oldgerman/SAU-G0/Data/Images/20220714_SAU-G0-GL_9小时500+次采集.png

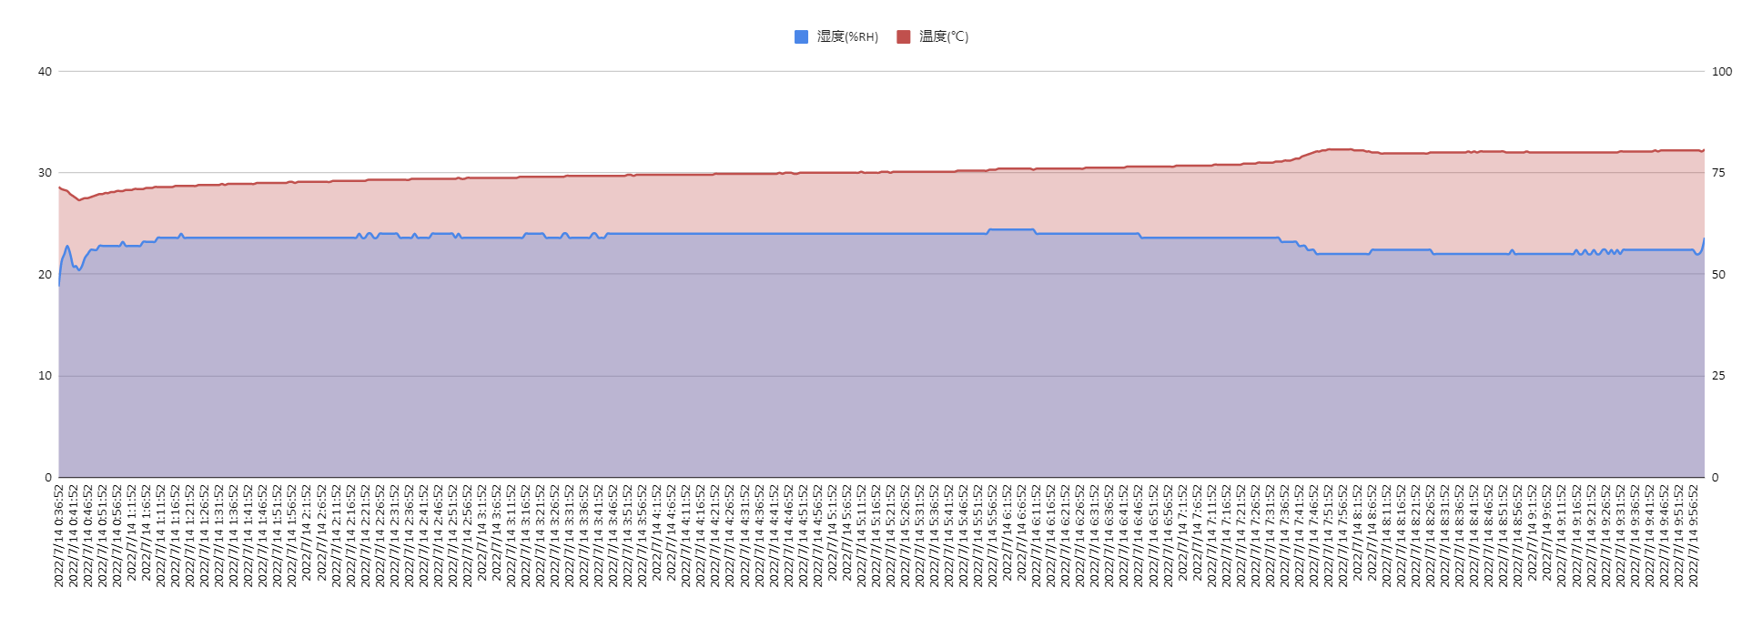
Data/Images/20220714_SAU-G0-GL_9小时500+次采集.png
