oldgerman/SAU-G0/Data/Images/20240409-20240522_SAU-G0-PL_43天2000+次采集2.png

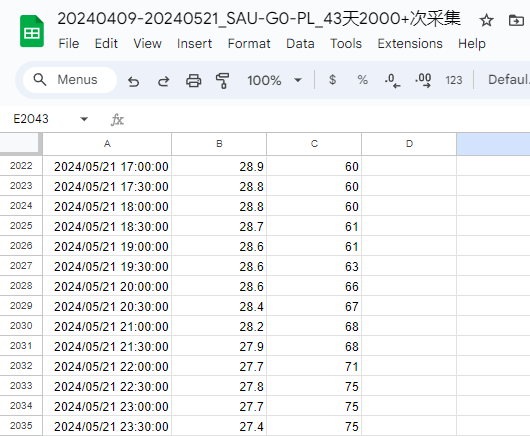
Data/Images/20240409-20240522_SAU-G0-PL_43天2000+次采集2.png
