oldgerman/SAU-G0/Data/Images/20240830-20240913_SAU-G0-PL_14天2043次采集.png

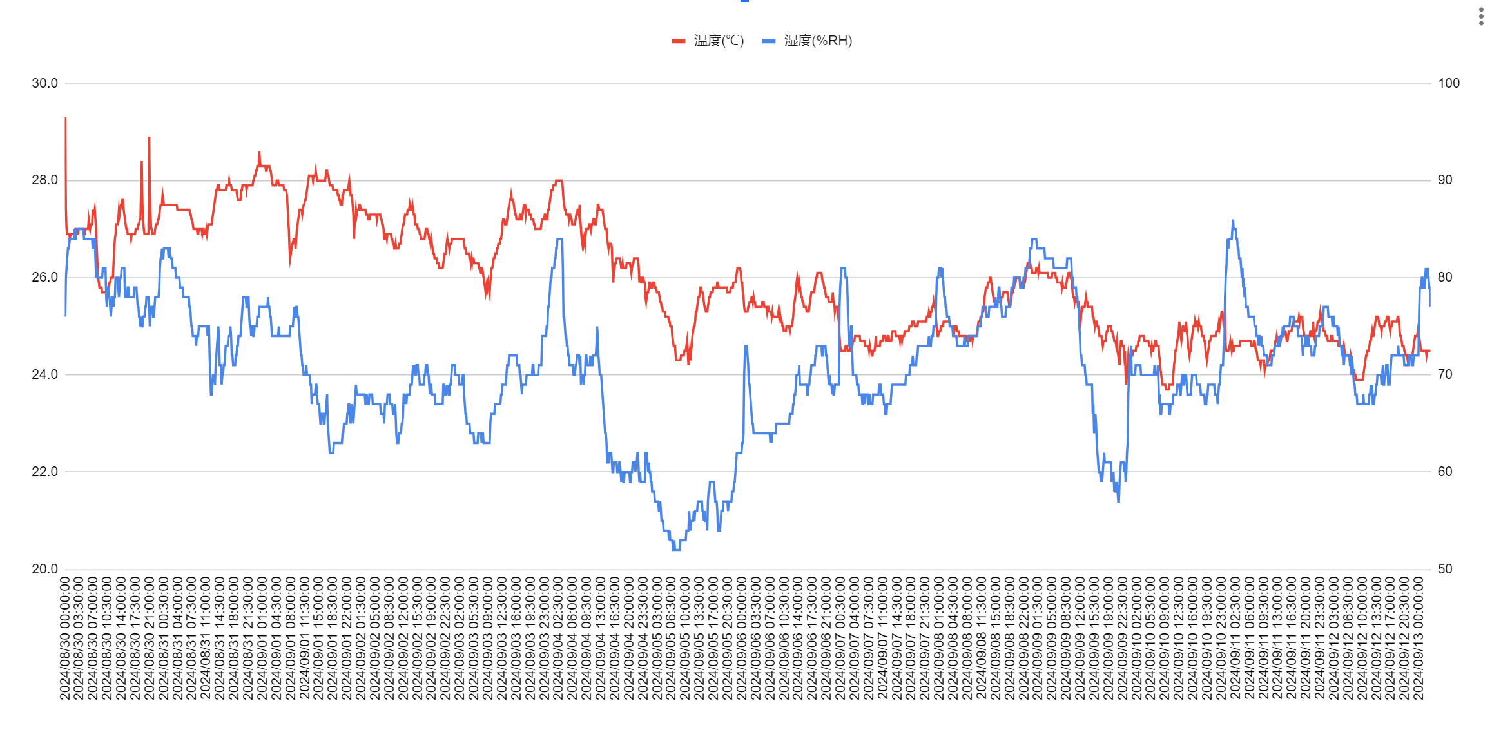
Data/Images/20240830-20240913_SAU-G0-PL_14天2043次采集.png
