oldgerman/SAU-G0/Data/Images/折线图选择数据时Invalid报错的原因是数据是文本，没有格式化为数字(1).png

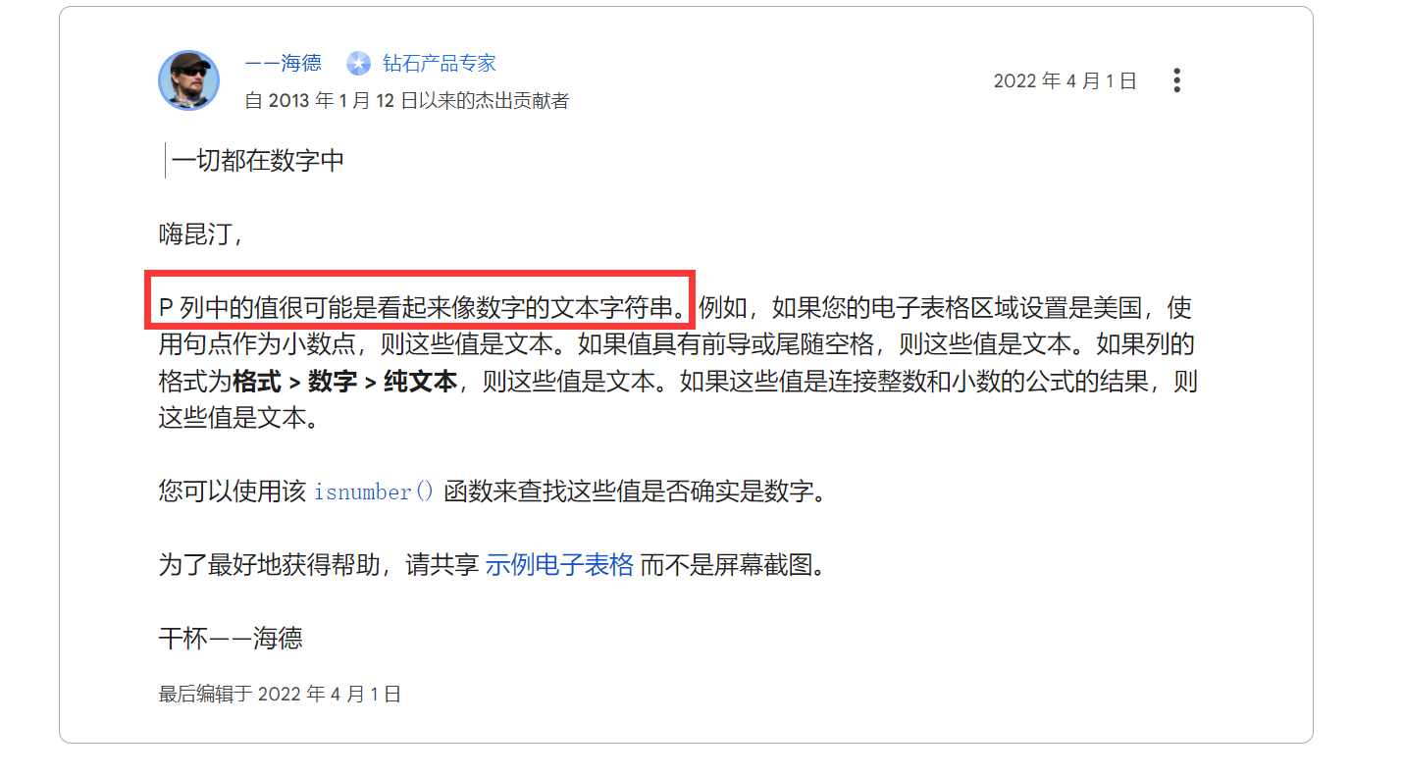
Data/Images/折线图选择数据时Invalid报错的原因是数据是文本，没有格式化为数字(1).png
