oldgerman/SAU-G0/Hardware/Datasheets/Diode/02_schaltplan_usb_ve-810x435-c-default.webp

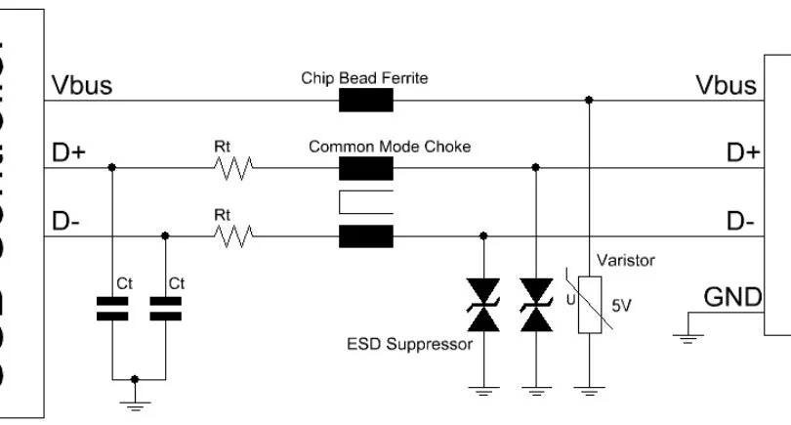
Hardware/Datasheets/Diode/02_schaltplan_usb_ve-810x435-c-default.webp
