oldgerman/SAU-G0/Hardware/Datasheets/Diode/2019-08-06_8-22-07.webp

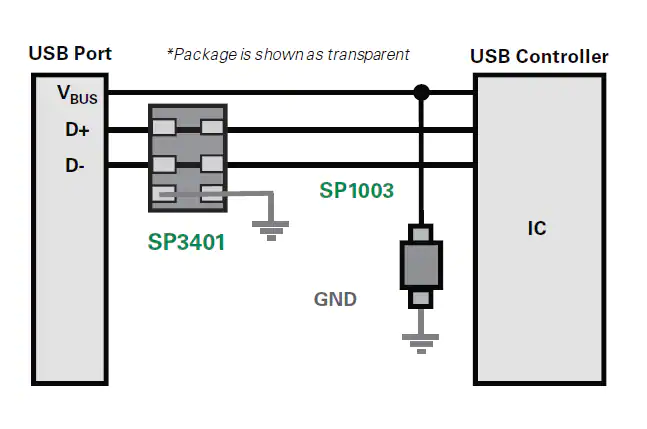
Hardware/Datasheets/Diode/2019-08-06_8-22-07.webp
