oldgerman/SAU-G0/Hardware/Datasheets/Diode/images.jpg

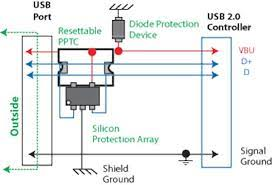
Hardware/Datasheets/Diode/images.jpg
