oldgerman/SAU-G0/Hardware/Datasheets/Diode/USB_2.0_Protection.jpg

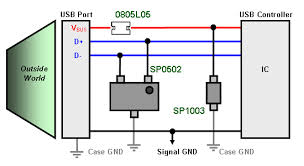
Hardware/Datasheets/Diode/USB_2.0_Protection.jpg
