oldgerman/SAU-G0/Hardware/Datasheets/Diode/vKJi6.png

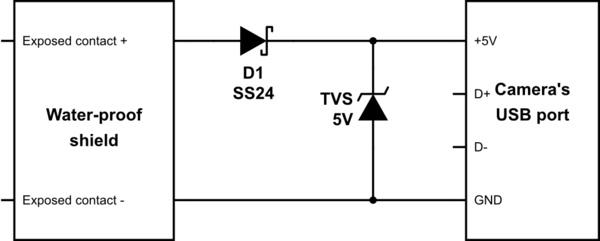
Hardware/Datasheets/Diode/vKJi6.png
