oldgerman/SAU-G0/Hardware/Datasheets/EEPROM/意法半导体串行接口的EEPROM m24c、M95、m93c特性.jpg

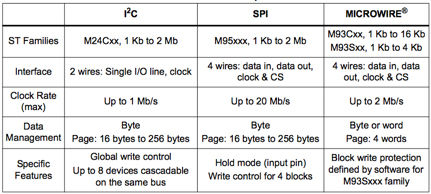
Hardware/Datasheets/EEPROM/意法半导体串行接口的EEPROM m24c、M95、m93c特性.jpg
