oldgerman/SAU-G0/Hardware/Datasheets/oled 0.66 16pin SPI/0.66 SSD1306 oled 尺寸图.jpg

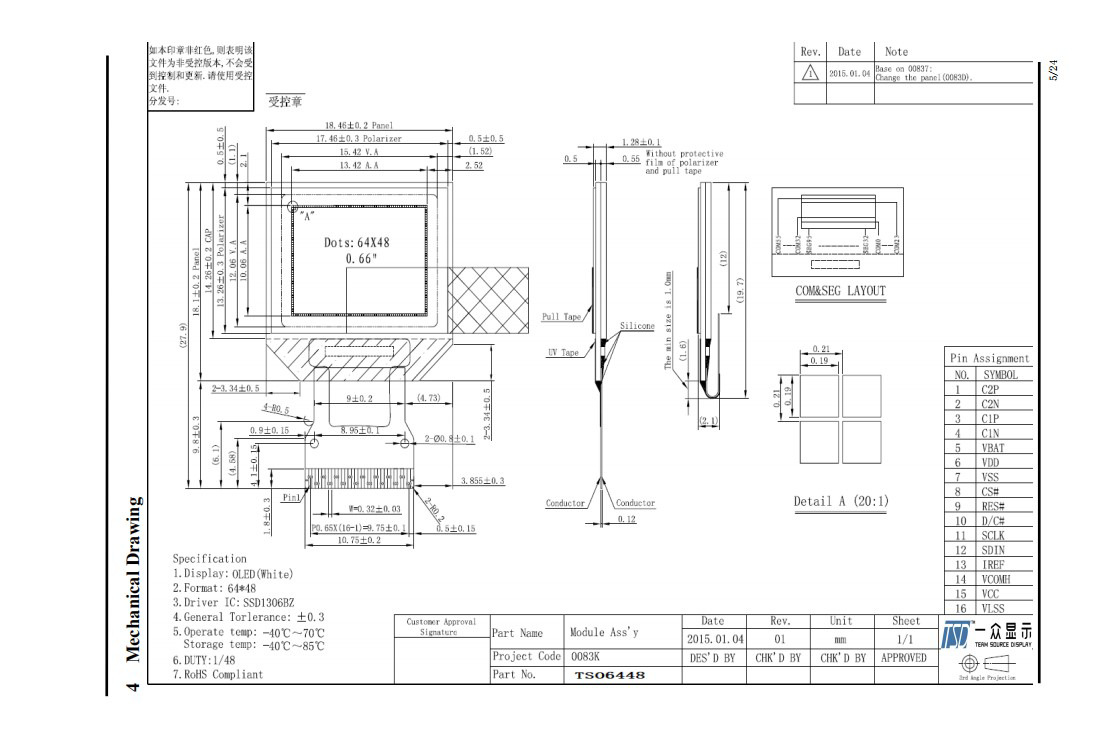
Hardware/Datasheets/oled 0.66 16pin SPI/0.66 SSD1306 oled 尺寸图.jpg
