oldgerman/SAU-G0/Hardware/Datasheets/oled 0.66 16pin SPI/外围电路.PNG

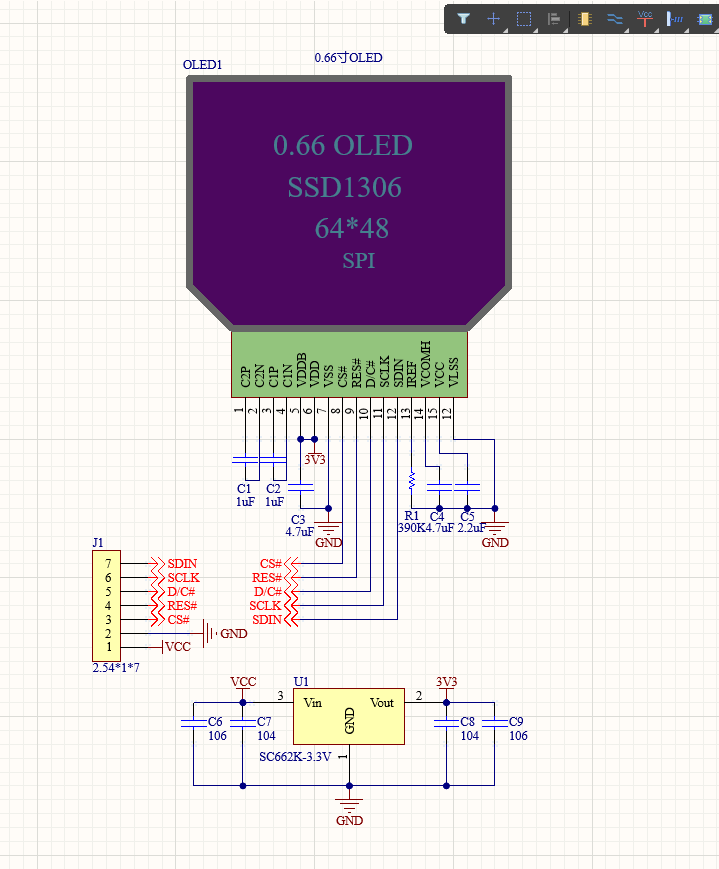
Hardware/Datasheets/oled 0.66 16pin SPI/外围电路.PNG
