oldgerman/SAU-G0/Hardware/Datasheets/RTC/DS3231/DS3231+EEPROM.png

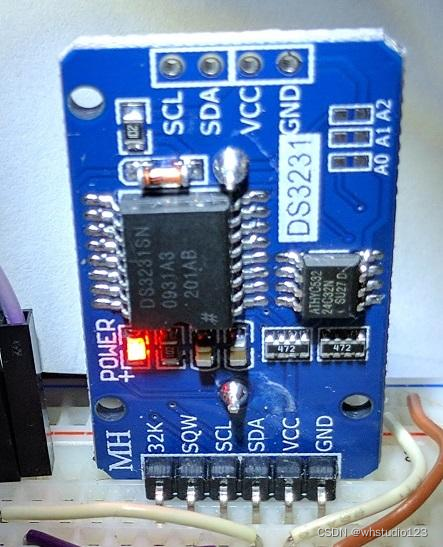
Hardware/Datasheets/RTC/DS3231/DS3231+EEPROM.png
