oldgerman/SAU-G0/Hardware/Datasheets/RTC/DS3231/images.jpg

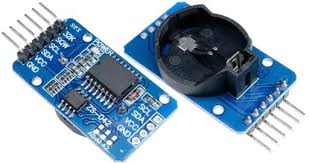
Hardware/Datasheets/RTC/DS3231/images.jpg
