oldgerman/SAU-G0/Hardware/Datasheets/RTC/PCF2129/FDK可充电电池_ML614R-TT31.png

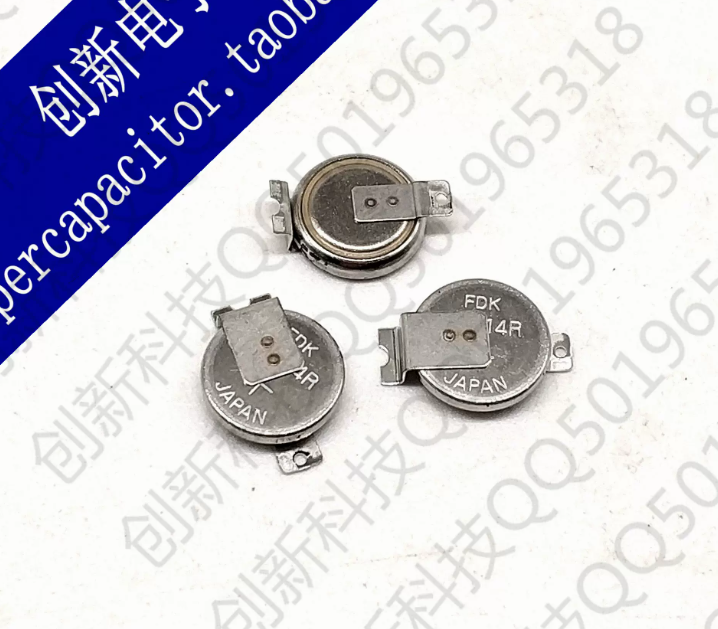
Hardware/Datasheets/RTC/PCF2129/FDK可充电电池_ML614R-TT31.png
