oldgerman/SAU-G0/Hardware/Datasheets/RTC/PCF2129/FDK可充电电池_ML系列产品线.png

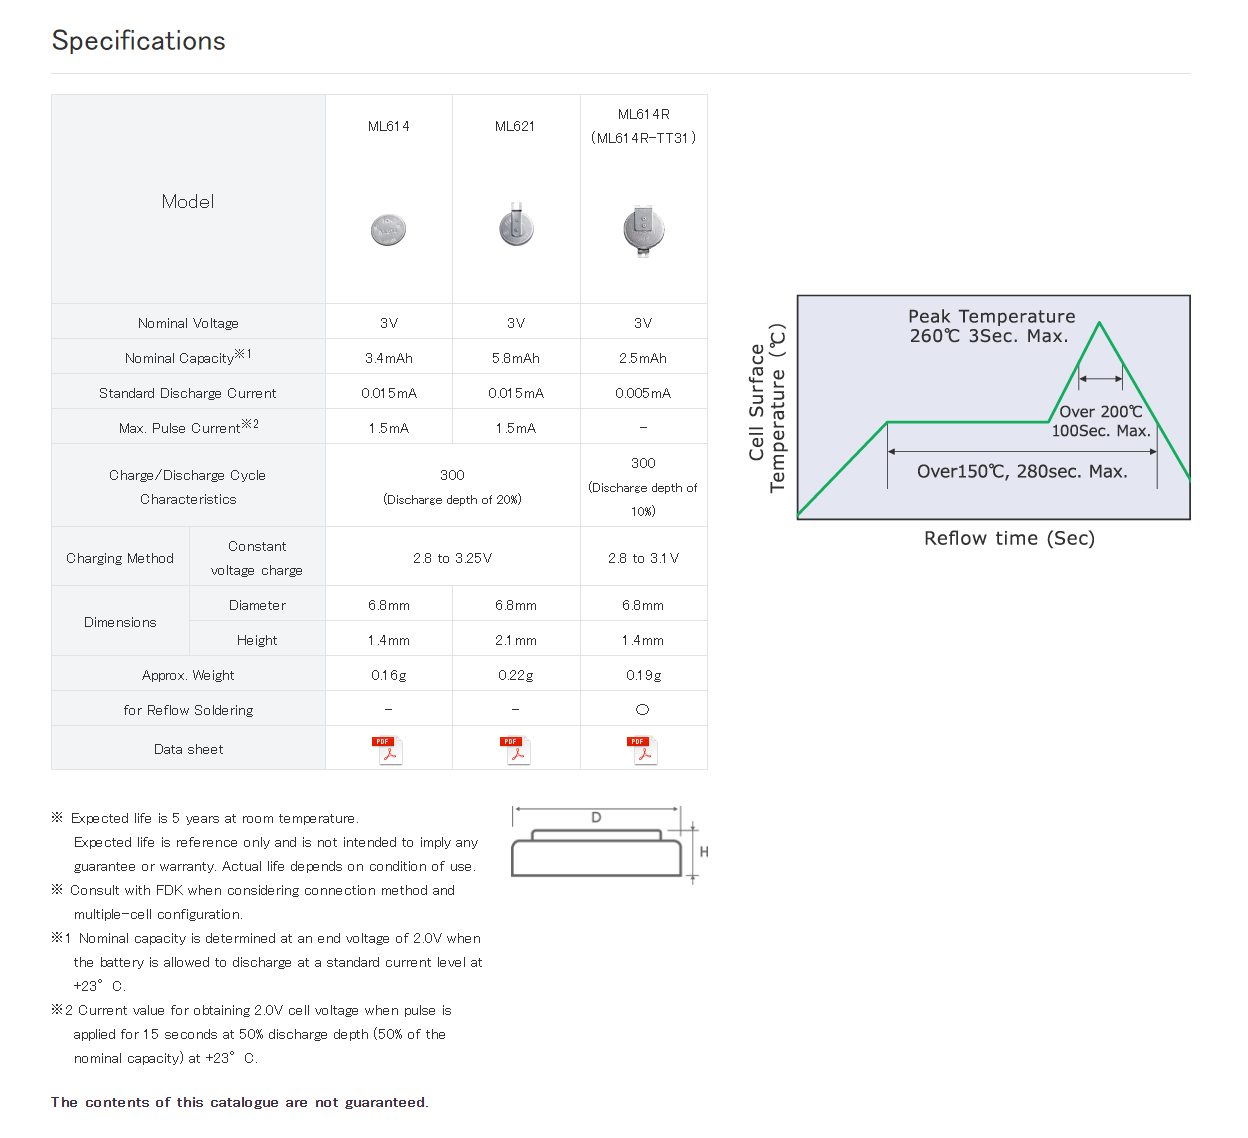
Hardware/Datasheets/RTC/PCF2129/FDK可充电电池_ML系列产品线.png
