oldgerman/SAU-G0/Hardware/Datasheets/RTC/PCF2129/image-1438068521577.jpg

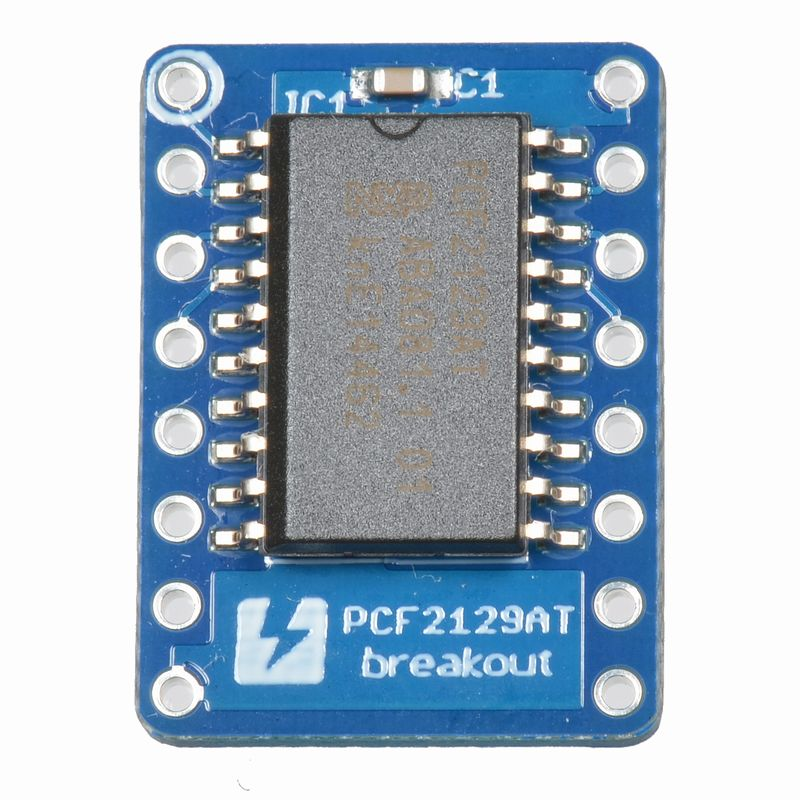
Hardware/Datasheets/RTC/PCF2129/image-1438068521577.jpg
