oldgerman/SAU-G0/Hardware/Datasheets/RTC/PCF2129/JST 614 Battery Holder, Button Contact.png

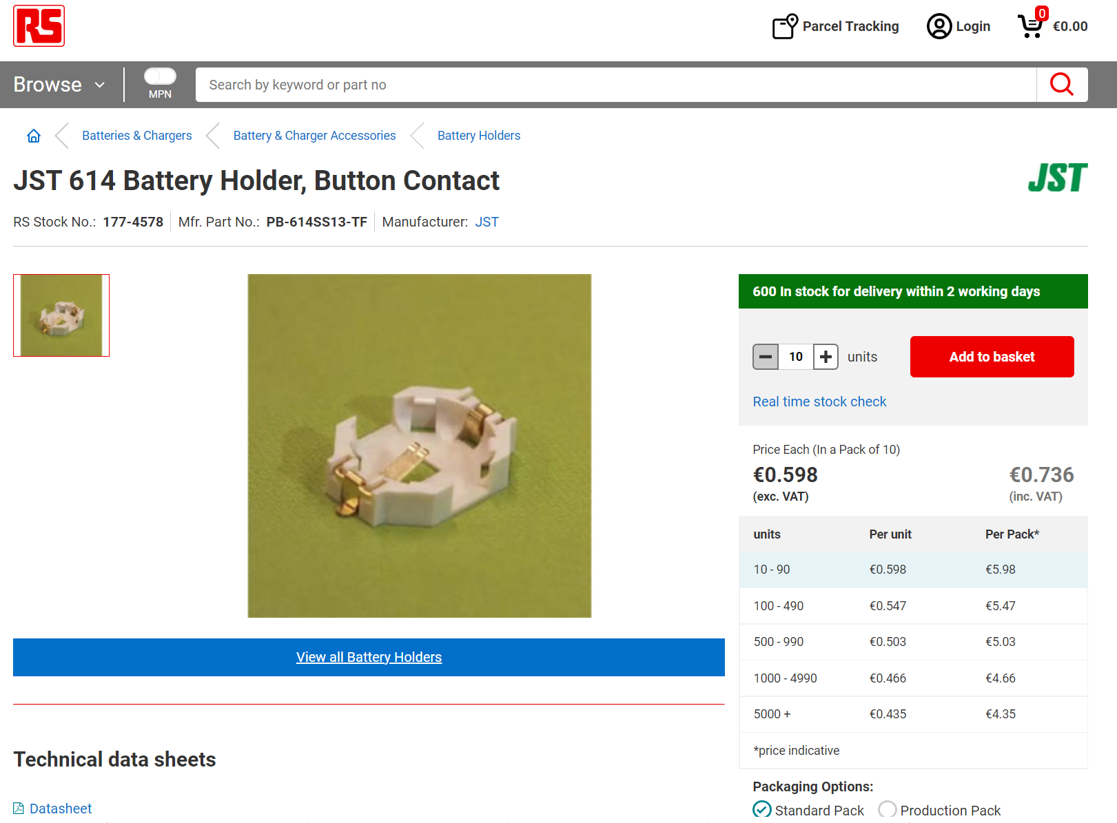
Hardware/Datasheets/RTC/PCF2129/JST 614 Battery Holder, Button Contact.png
