oldgerman/SAU-G0/Hardware/Datasheets/RTC/PCF2129/MS518SE-patch-connector.jpg

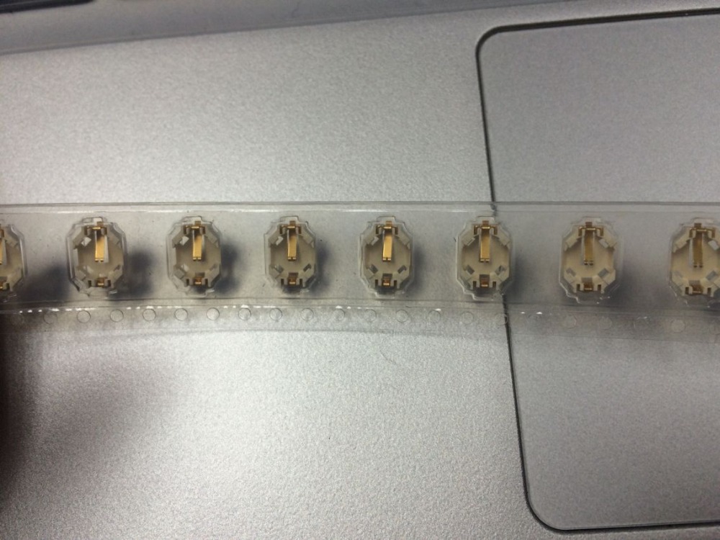
Hardware/Datasheets/RTC/PCF2129/MS518SE-patch-connector.jpg
