oldgerman/SAU-G0/Hardware/Datasheets/RTC/PCF2129/MS518SE-PCB焊接-注意电池下方禁止布线区.jpg

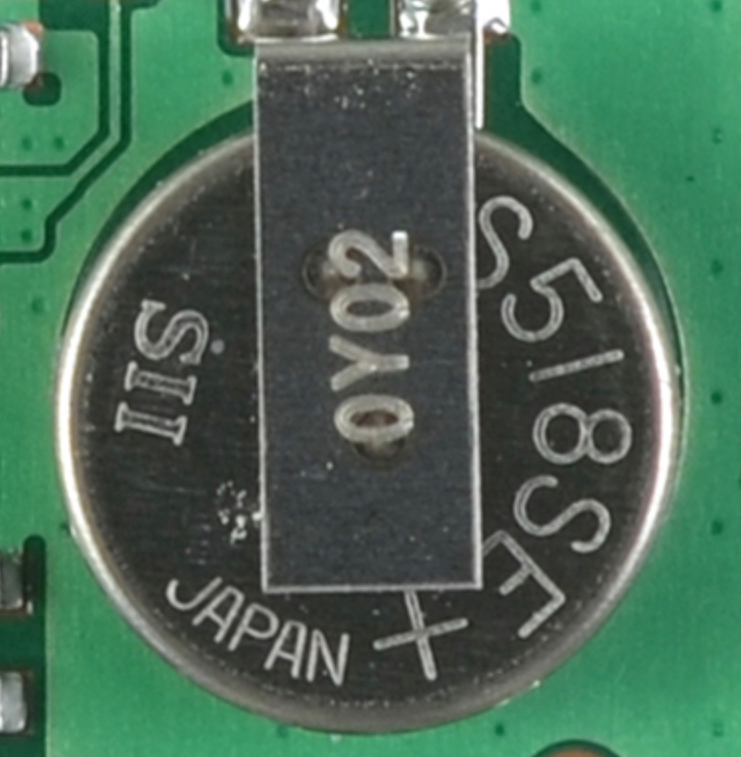
Hardware/Datasheets/RTC/PCF2129/MS518SE-PCB焊接-注意电池下方禁止布线区.jpg
