oldgerman/SAU-G0/Hardware/Datasheets/RTC/PCF2129/MS518SE背面焊盘.jpg

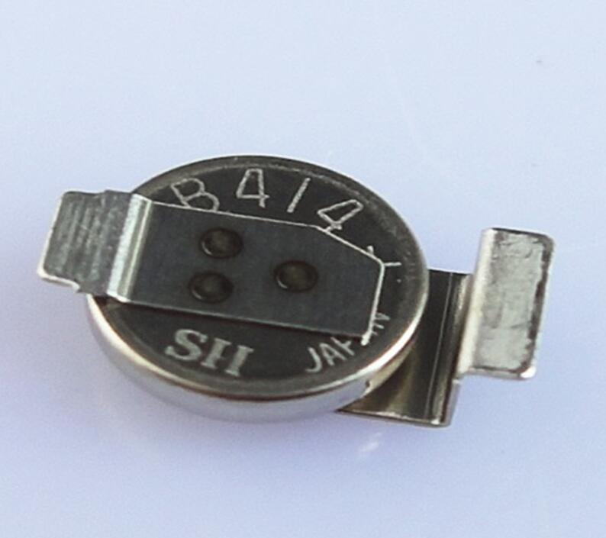
Hardware/Datasheets/RTC/PCF2129/MS518SE背面焊盘.jpg
