oldgerman/SAU-G0/Hardware/Datasheets/RTC/PCF2129/MS621FE.png

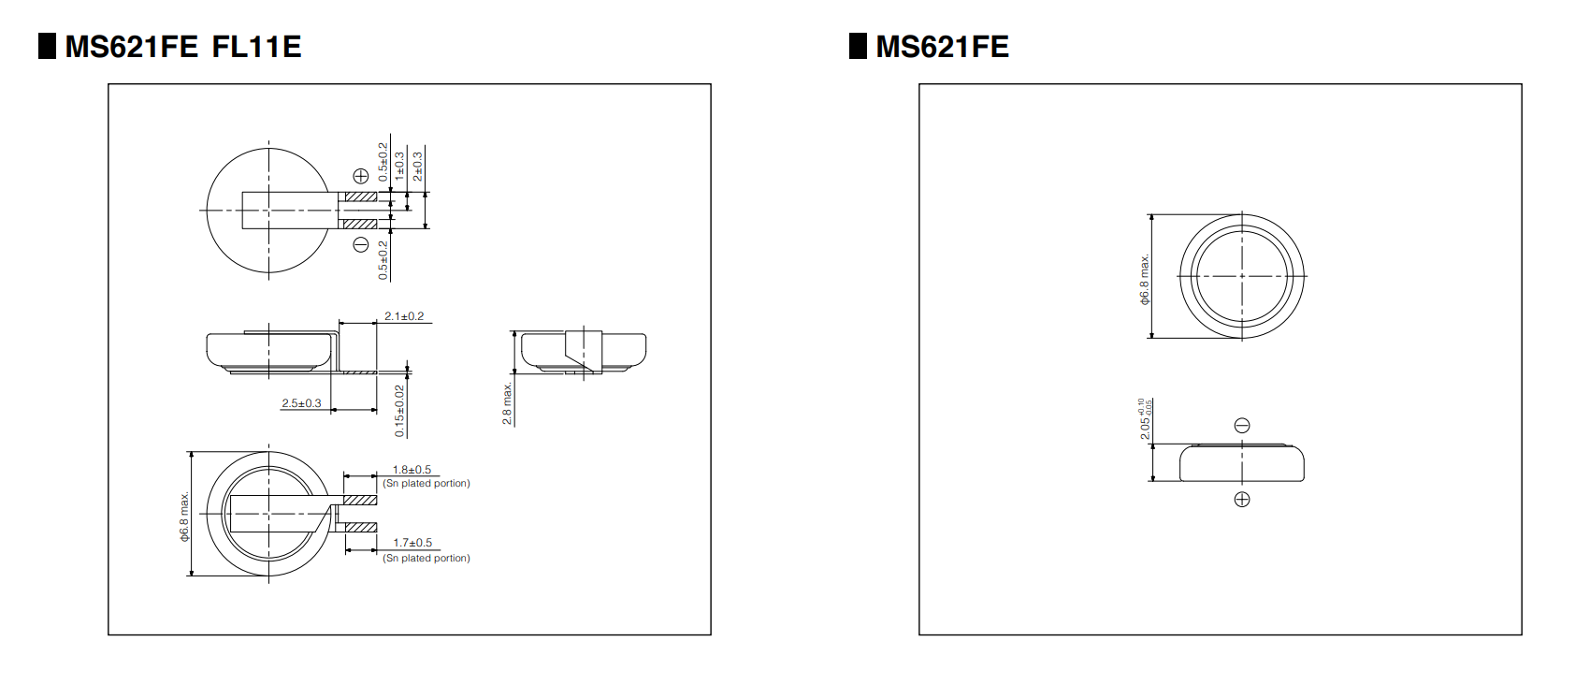
Hardware/Datasheets/RTC/PCF2129/MS621FE.png
