oldgerman/SAU-G0/Hardware/Datasheets/RTC/PCF2129/MS621FE电池充电电路.png

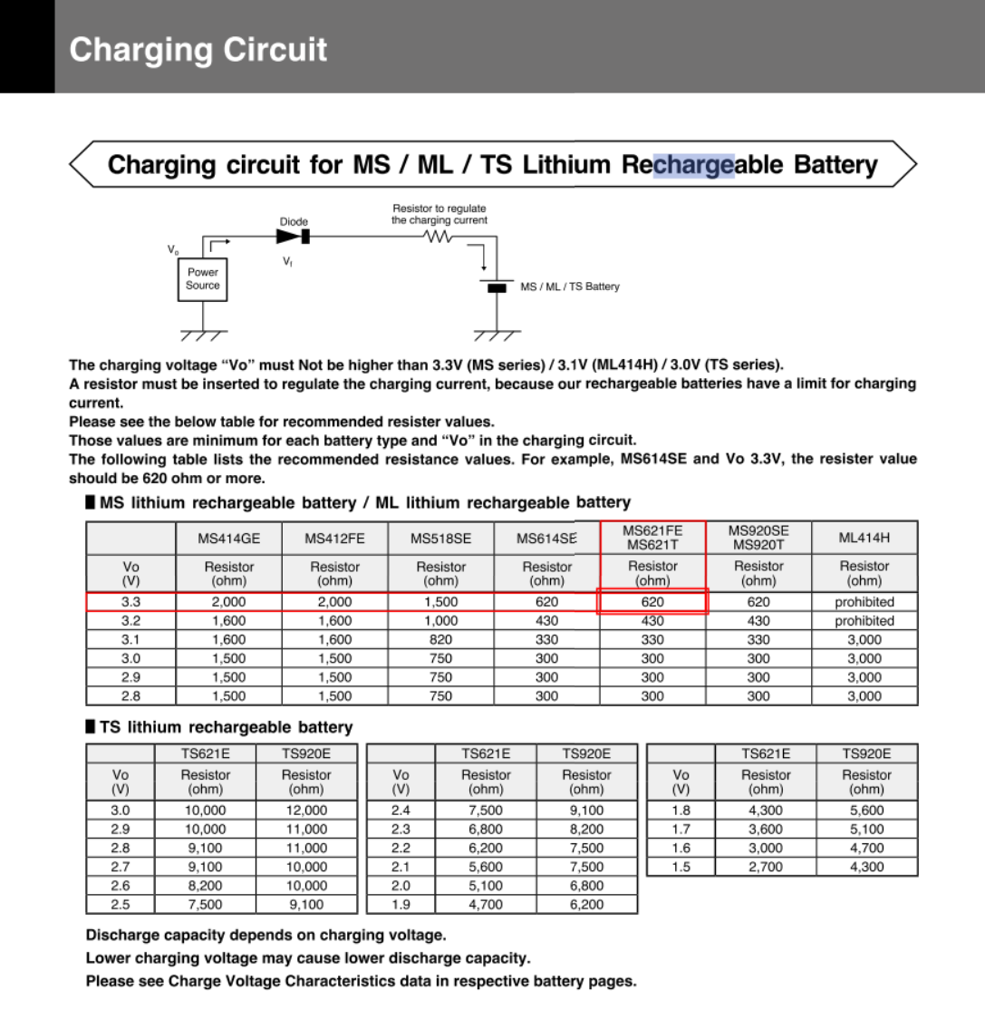
Hardware/Datasheets/RTC/PCF2129/MS621FE电池充电电路.png
