oldgerman/SAU-G0/Hardware/Datasheets/RTC/PCF2129/pcf2129_model.png

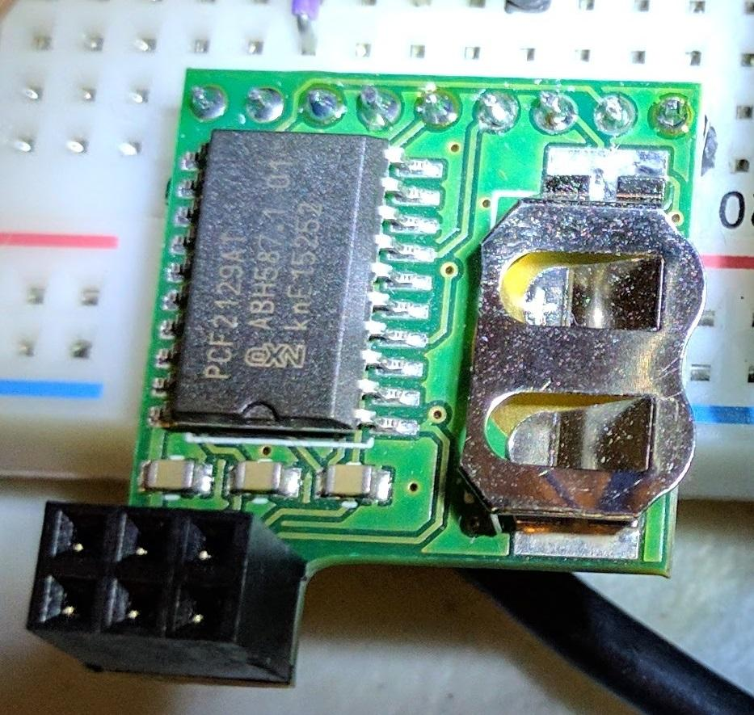
Hardware/Datasheets/RTC/PCF2129/pcf2129_model.png
