oldgerman/SAU-G0/Hardware/Datasheets/RTC/PCF2129/PCF2129后备电池.jpeg

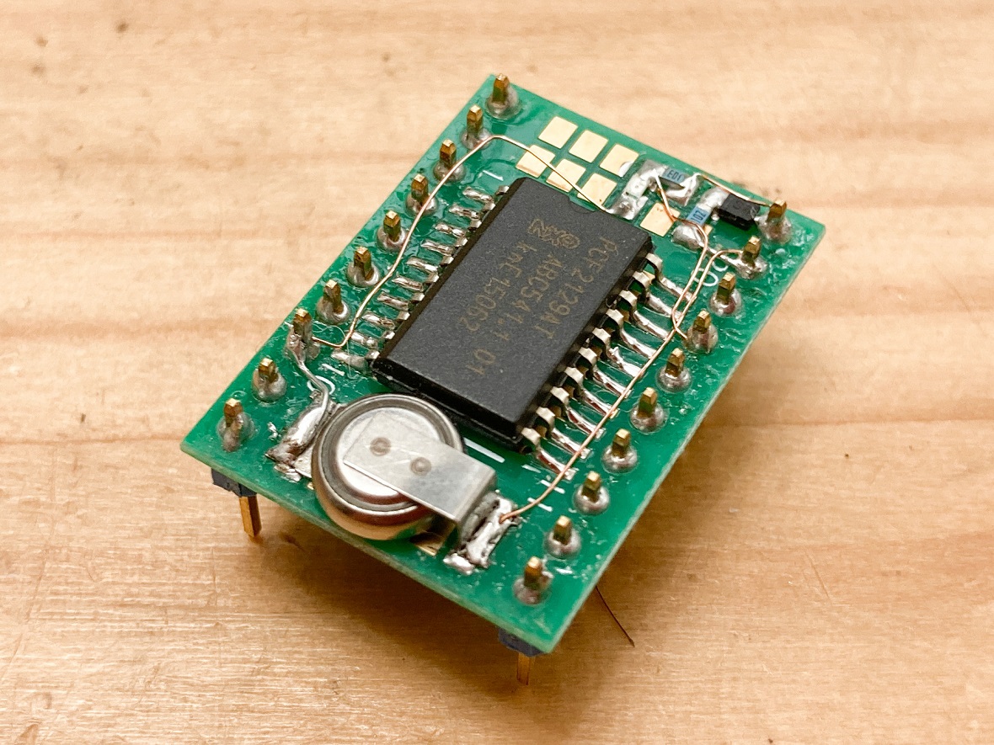
Hardware/Datasheets/RTC/PCF2129/PCF2129后备电池.jpeg
