oldgerman/SAU-G0/Hardware/Datasheets/RTC/PCF2129/RTC circuit.jpg

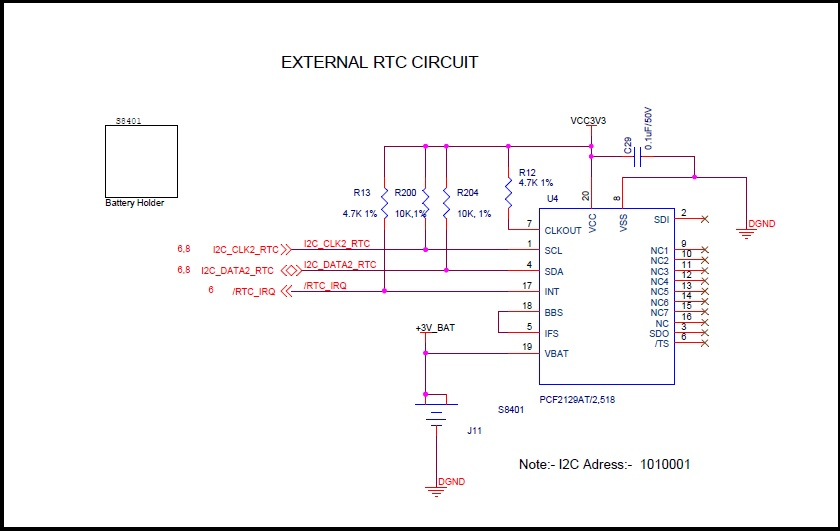
Hardware/Datasheets/RTC/PCF2129/RTC circuit.jpg
