oldgerman/SAU-G0/Hardware/Datasheets/RTC/PCF2129/ScreenShot-2021-05-13-12.09.35.png

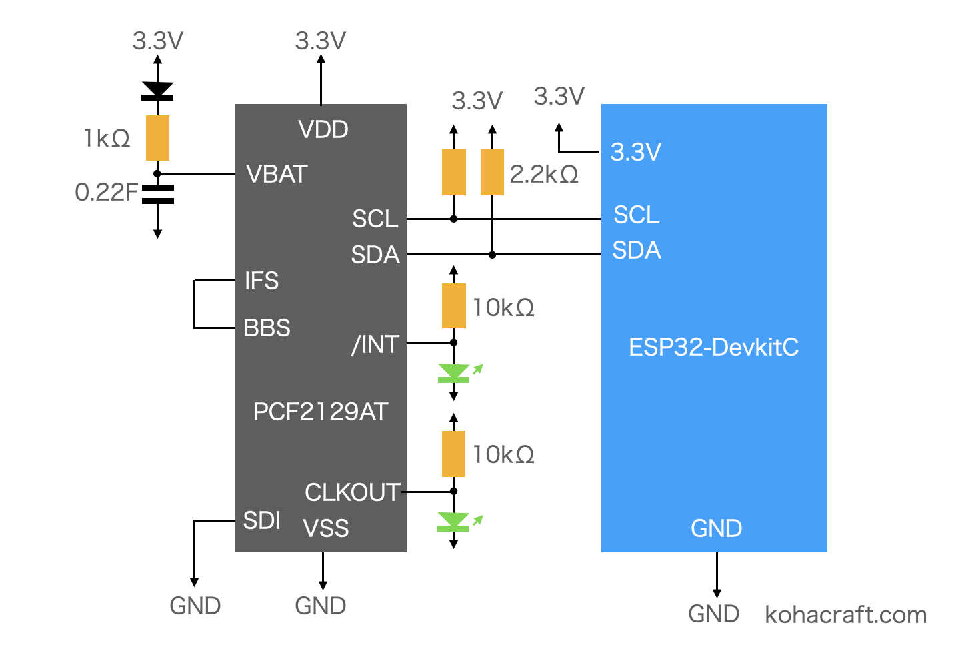
Hardware/Datasheets/RTC/PCF2129/ScreenShot-2021-05-13-12.09.35.png
