oldgerman/SAU-G0/Hardware/Datasheets/RTC/PCF2129/传感器板尺寸布局，矩形是JST 518 纽扣电池座使用MS518，大的圆是MS621.png

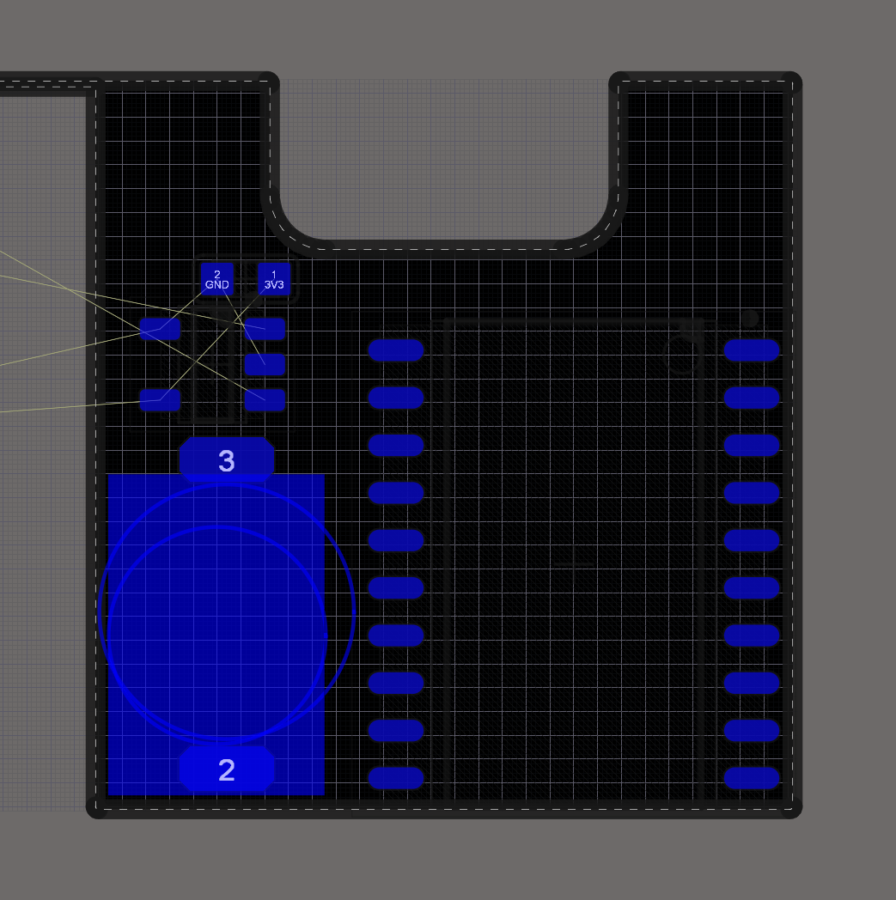
Hardware/Datasheets/RTC/PCF2129/传感器板尺寸布局，矩形是JST 518 纽扣电池座使用MS518，大的圆是MS621.png
