oldgerman/SAU-G0/Hardware/Datasheets/RTC/PCF2129/纽扣电池正负极.jpg

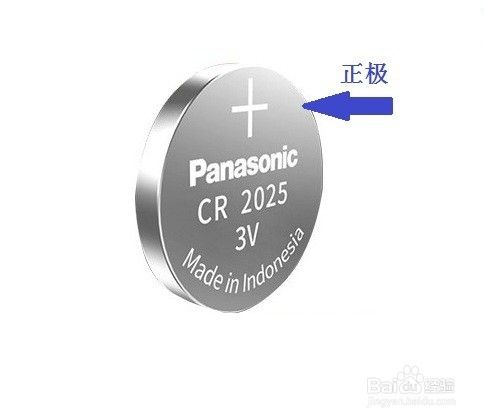
Hardware/Datasheets/RTC/PCF2129/纽扣电池正负极.jpg
