oldgerman/SAU-G0/Hardware/Datasheets/TYPE-C/USBTypeCPinOutDiagram.jpg

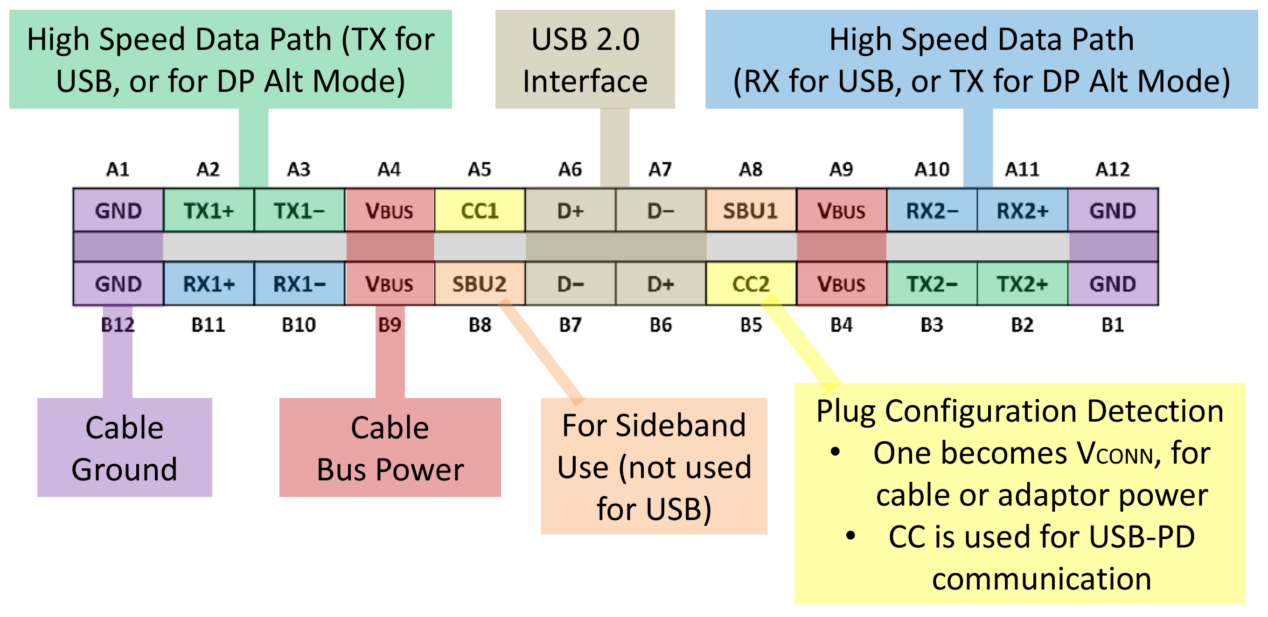
Hardware/Datasheets/TYPE-C/USBTypeCPinOutDiagram.jpg
