oldgerman/SAU-G0/Hardware/Datasheets/有源晶振/G031使用外部有源晶振时，enable引脚是可选的.png

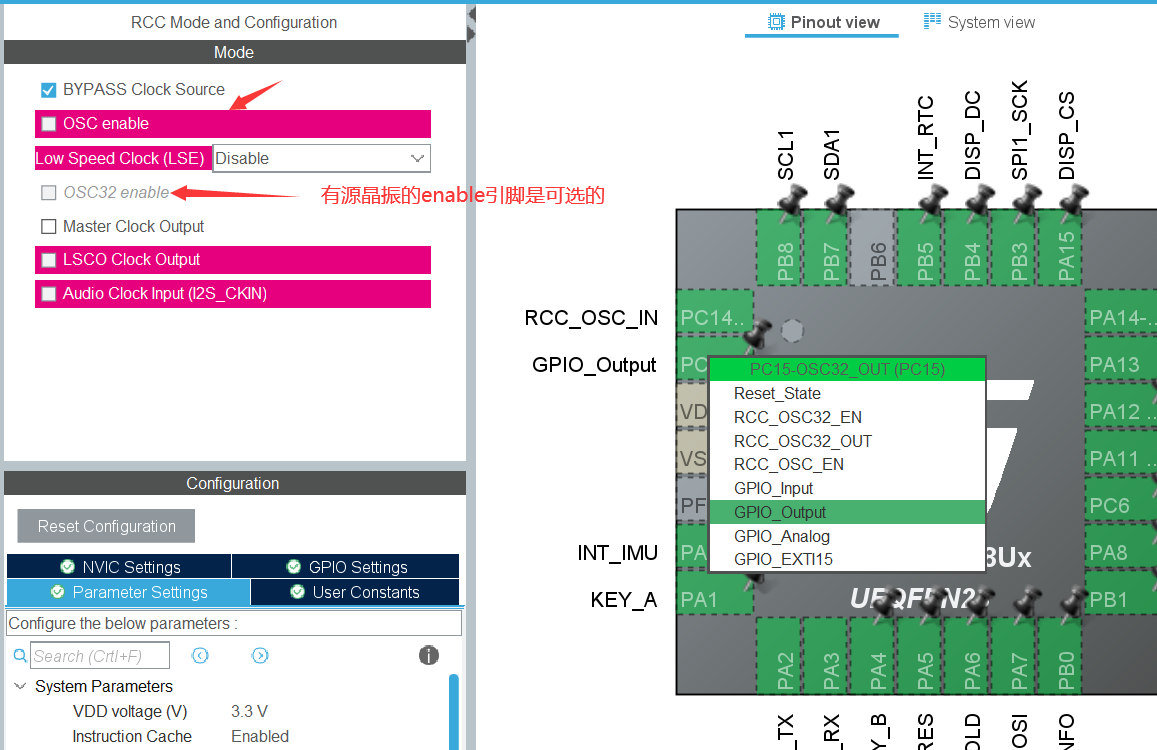
Hardware/Datasheets/有源晶振/G031使用外部有源晶振时，enable引脚是可选的.png
