oldgerman/SAU-G0/Hardware/Datasheets/有源晶振/STM32F769I-DISO板的NZ2520SB用作HSE_只用到了一个OSC引脚.png

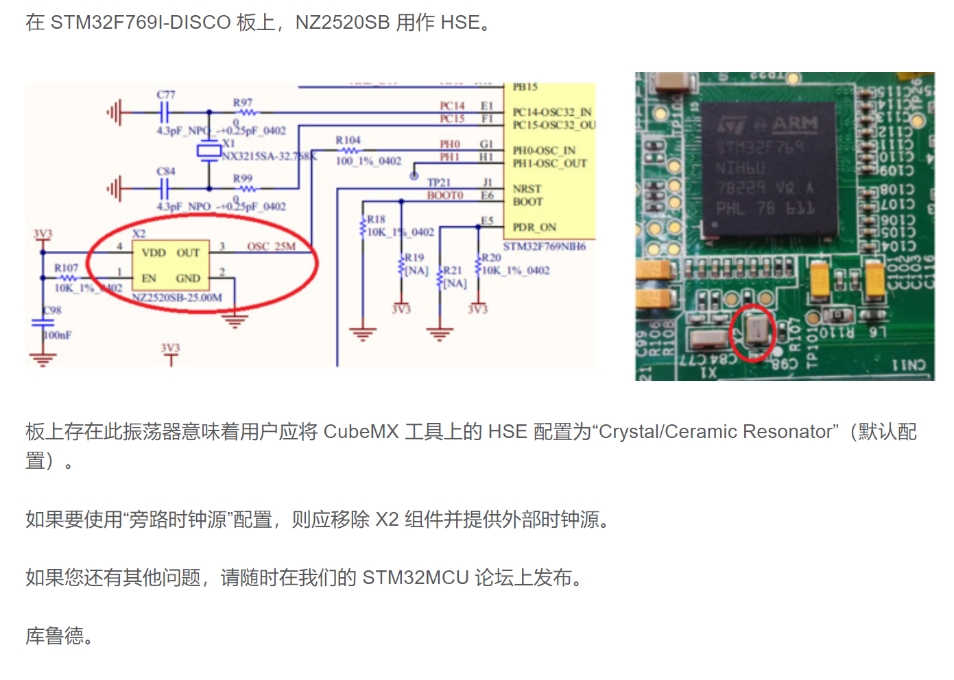
Hardware/Datasheets/有源晶振/STM32F769I-DISO板的NZ2520SB用作HSE_只用到了一个OSC引脚.png
