oldgerman/SAU-G0/Hardware/Datasheets/有源晶振/外围电路.jpg

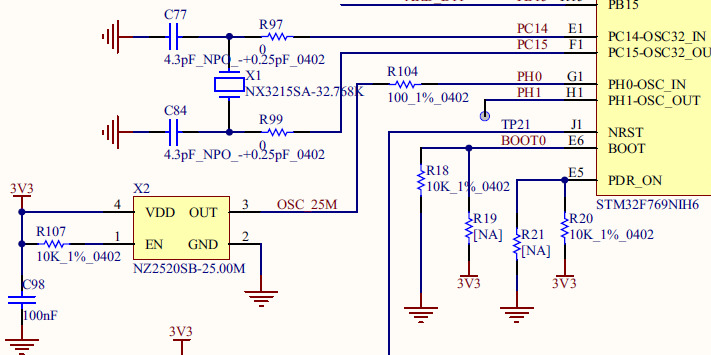
Hardware/Datasheets/有源晶振/外围电路.jpg
