oldgerman/SAU-G0/Hardware/Datasheets/有源晶振/有源晶振外围电路1.jpeg

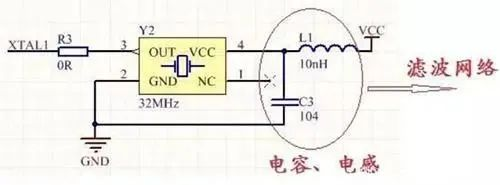
Hardware/Datasheets/有源晶振/有源晶振外围电路1.jpeg
