oldgerman/SAU-G0/Hardware/SW_Project/Size/JST_ZH1.5_2P_胶壳-2.png

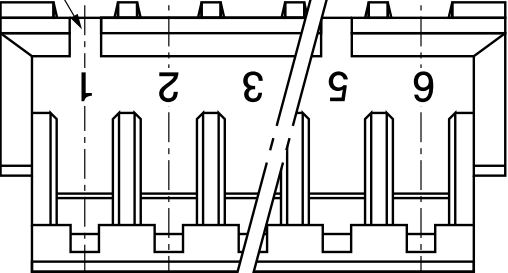
Hardware/SW_Project/Size/JST_ZH1.5_2P_胶壳-2.png
