oldgerman/SAU-G0/Hardware/SW_Project/Size/按键FPC焊盘特写_PFC宽度4mm.JPG

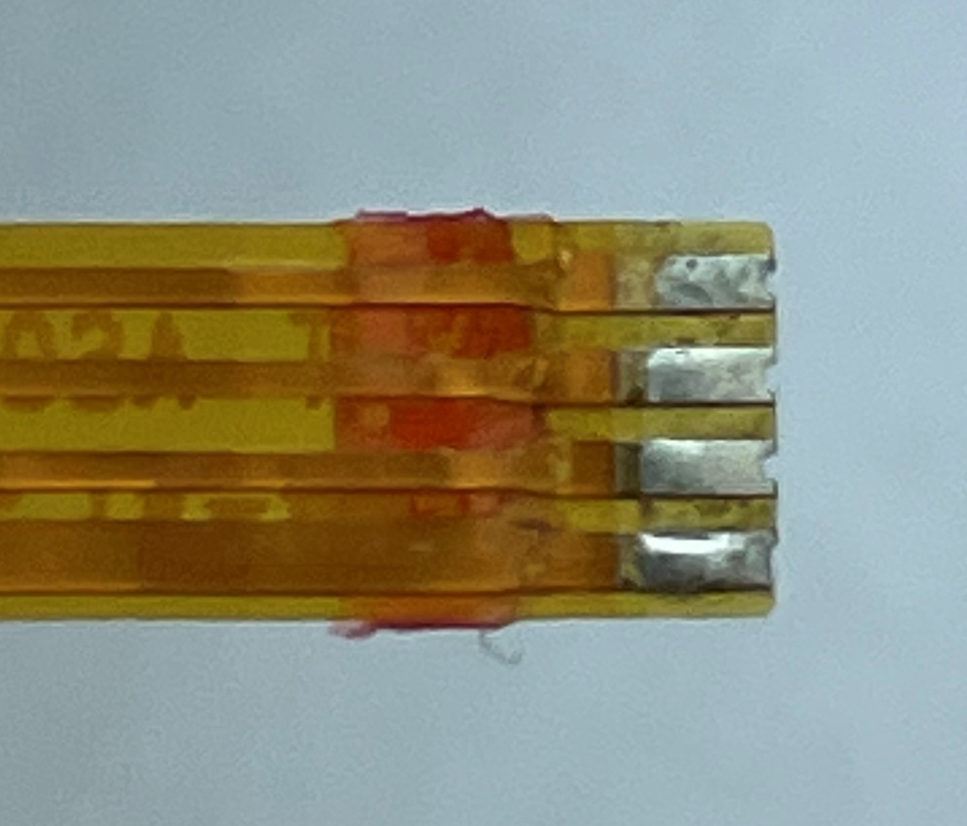
Hardware/SW_Project/Size/按键FPC焊盘特写_PFC宽度4mm.JPG
