oldgerman/SAU-G0/Images/SAU-G0-EVM_实物.jpg

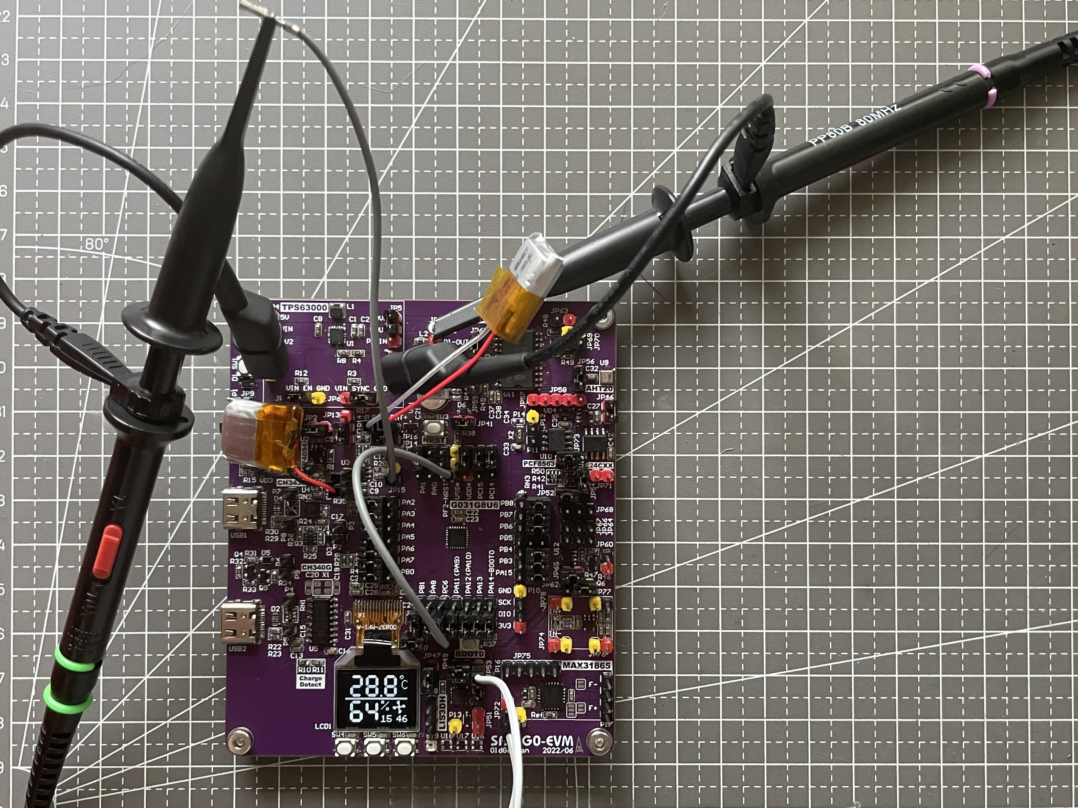
Images/SAU-G0-EVM_实物.jpg
