oldgerman/SAU-G0/Images/SAU-G0_2号机3.PNG

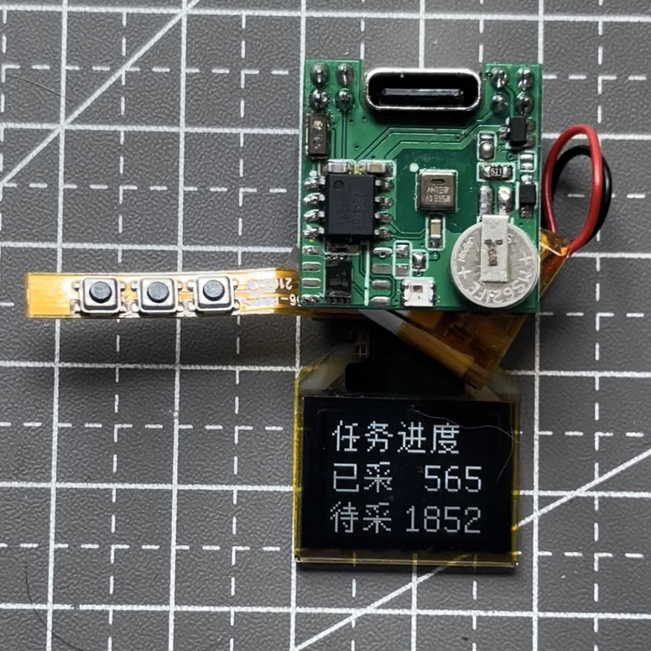
Images/SAU-G0_2号机3.PNG
