oldgerman/SAU-G0/Images/XCOM连接串口黑屏就勾选DTR和RTS，长按中键连接.png

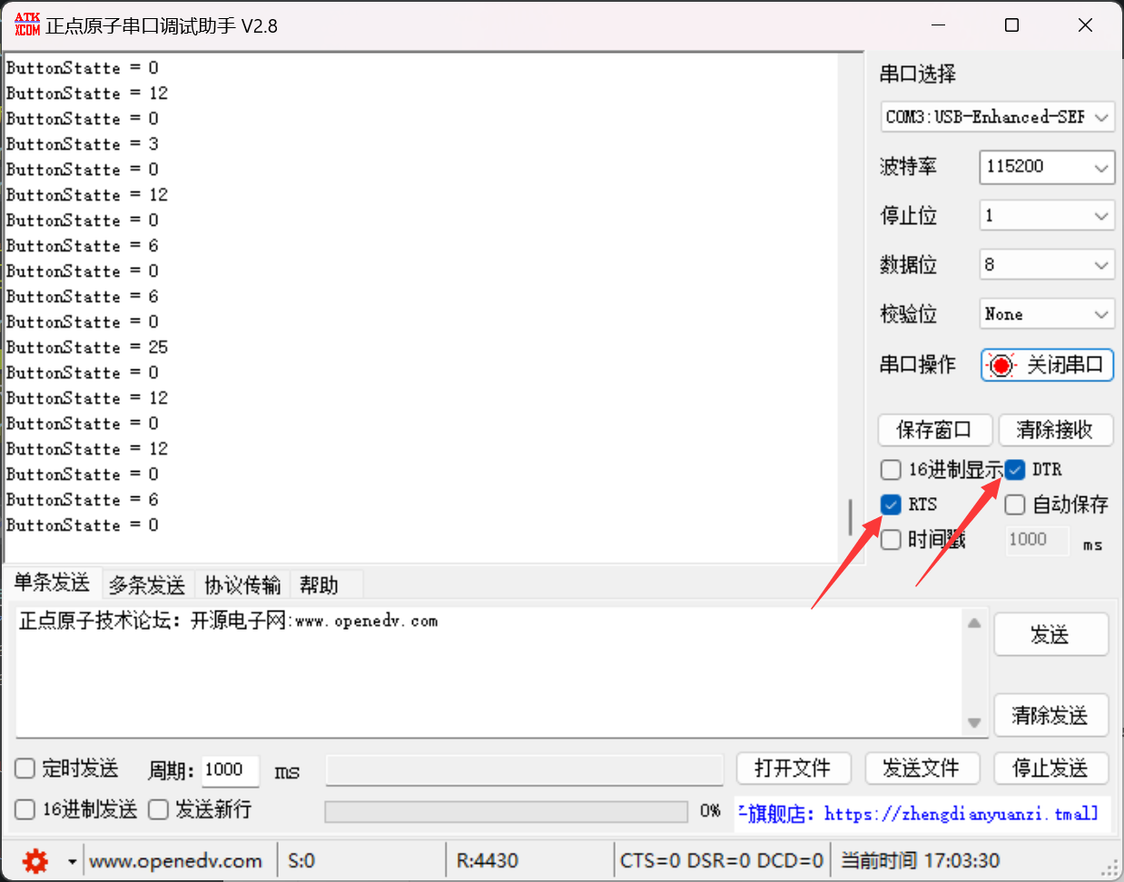
Images/XCOM连接串口黑屏就勾选DTR和RTS，长按中键连接.png
