oldgerman/SAU-G0/Images/得从豆总的电子烟主板的车上面拆OLED和FPC按键.jpg

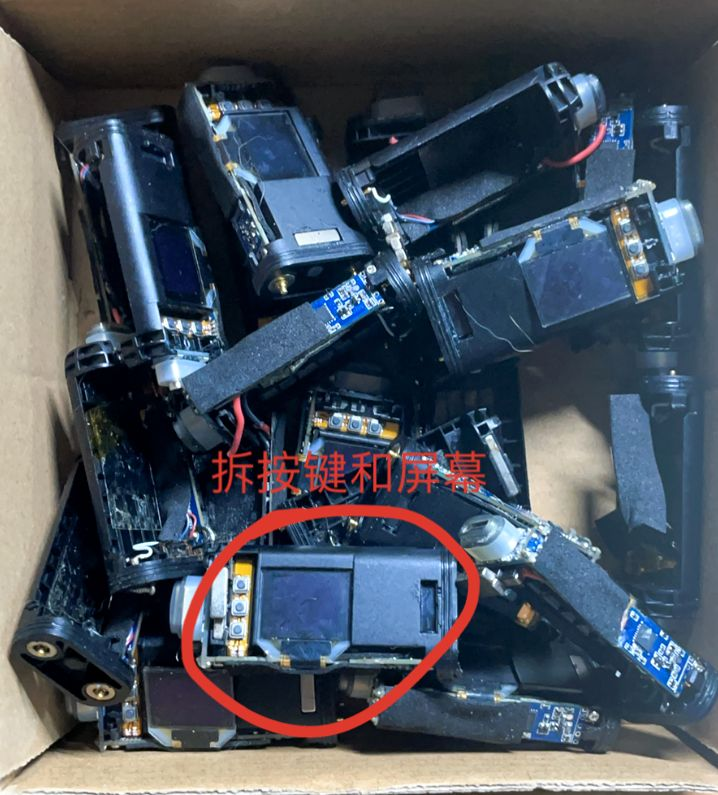
Images/得从豆总的电子烟主板的车上面拆OLED和FPC按键.jpg
