oldgerman/SAU-G0/Images/掌中大小.jpg

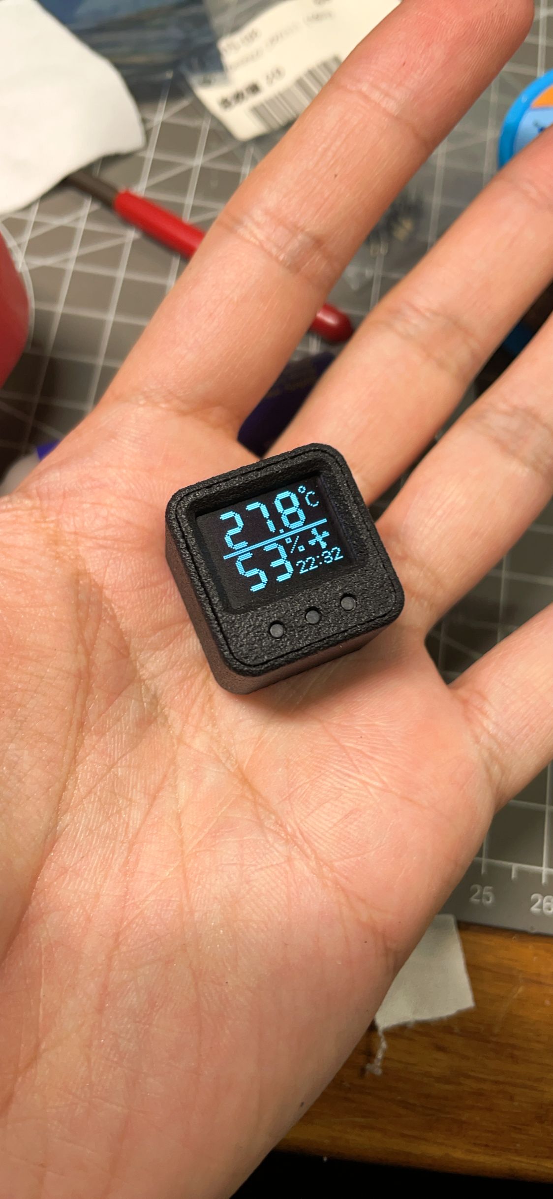
Images/掌中大小.jpg
