oldgerman/SAU-G0/朋友们下车的成品/20240410_快修侠_SAU-G031G8U6_GL(1).jpg

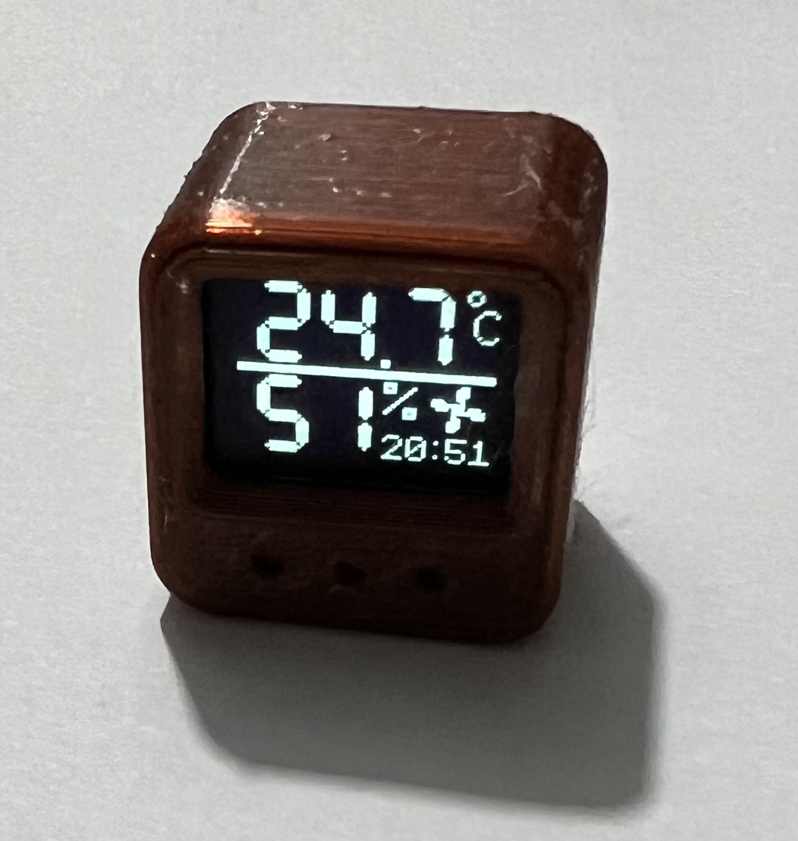
朋友们下车的成品/20240410_快修侠_SAU-G031G8U6_GL(1).jpg
