oldgerman/SAU-G0/朋友们下车的成品/20240430_豆总_SAU-G031G8U6_PL(2).jpg

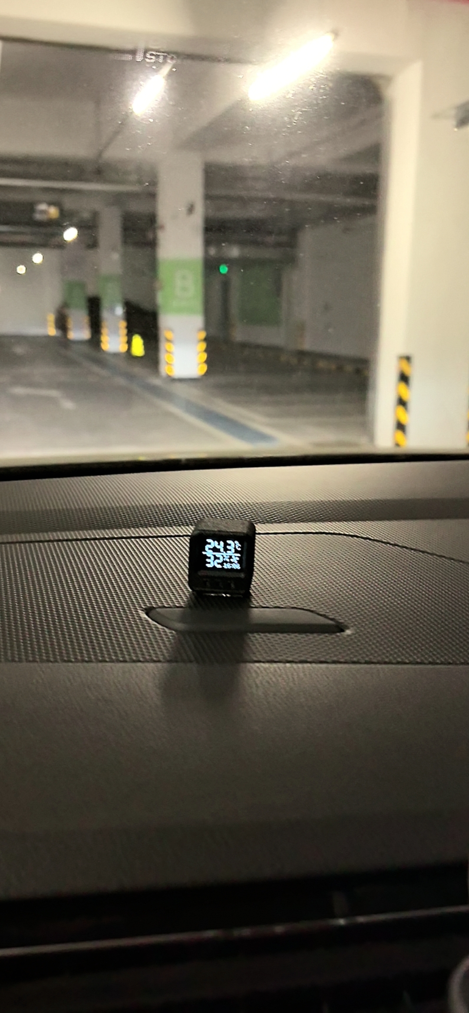
朋友们下车的成品/20240430_豆总_SAU-G031G8U6_PL(2).jpg
