oldgerman/SAU-G0/Hardware/SW_Project/DXF_OUT/PCB_2.DXF

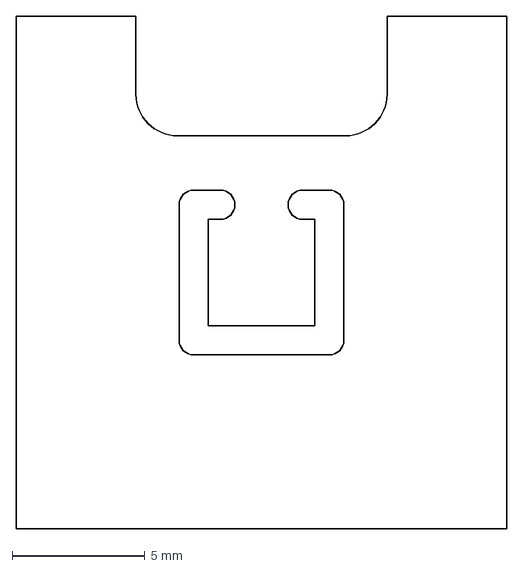
[picture p110: CAD file, 2024-04-08]
Hardware/SW_Project/DXF_OUT/PCB_2.DXF
18.5 x 19.3 mm
