oldgerman/SAU-G0/Hardware/SW_Project/STEP_OUT/2.00mm母座2x2.STEP

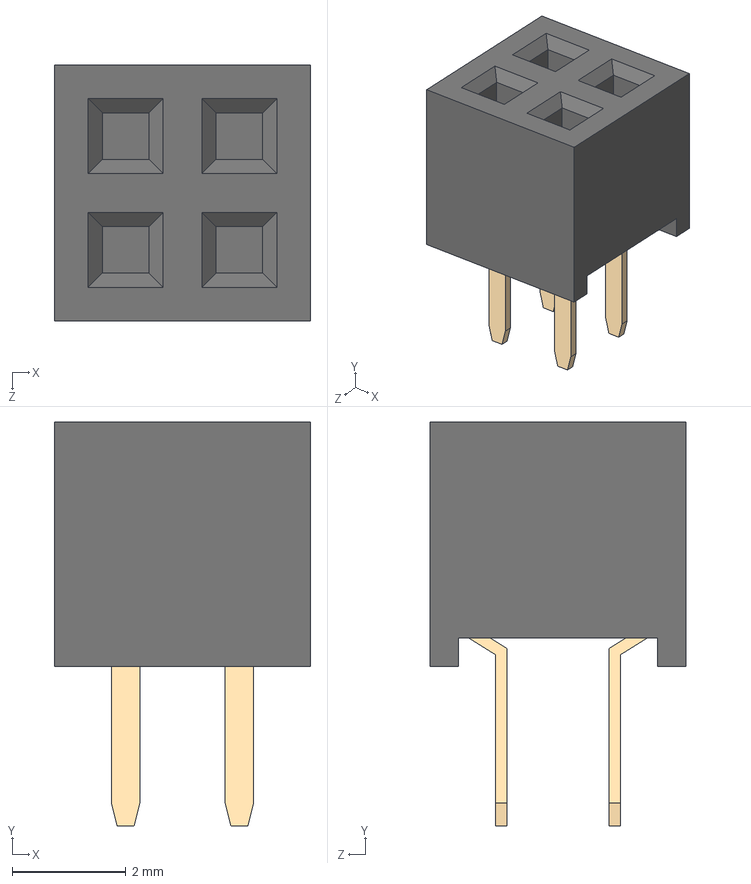
[picture p111: CAD file, 2024-04-08]
Hardware/SW_Project/STEP_OUT/2.00mm母座2x2.STEP
4.50 x 7.10 x 4.50 mm
