oldgerman/SAU-G0/Hardware/SW_Project/STL_OUT/连接零件/外壳-方案2-GL_LC打印_连接零件_连接杆1.5mm.STL

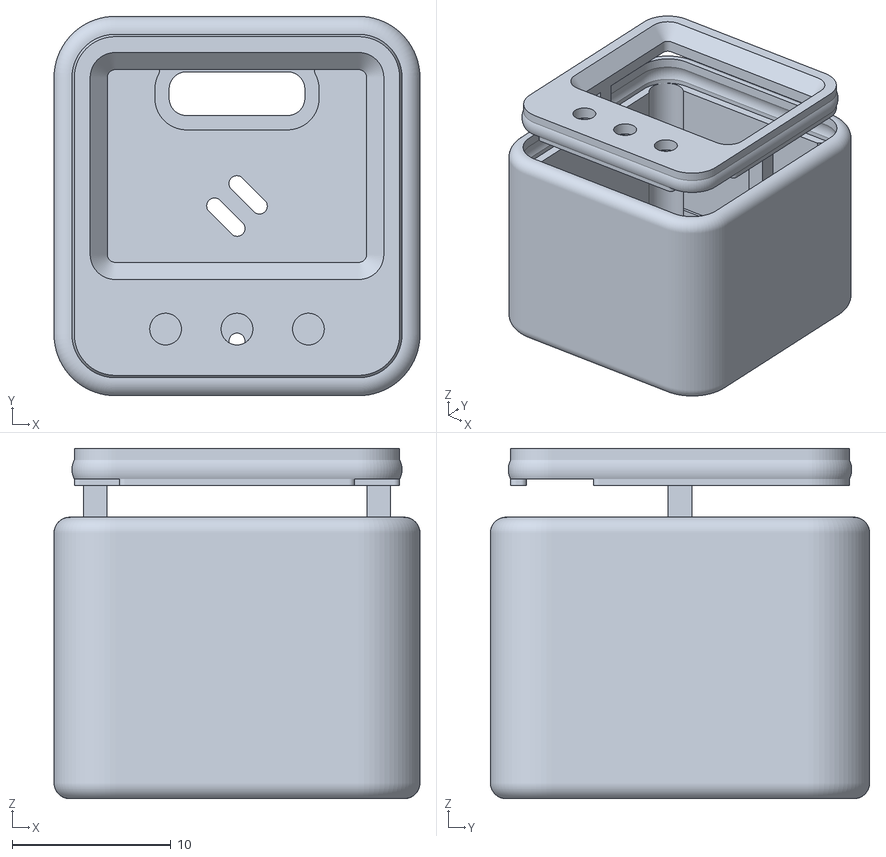
[picture p113: CAD file, 2024-04-08]
Hardware/SW_Project/STL_OUT/连接零件/外壳-方案2-GL_LC打印_连接零件_连接杆1.5mm.STL
23.1 x 23.9 x 22.1
