oldgerman/SAU-G0/Hardware/SW_Project/TYPE-C-14-vertical_H-10mm.SLDPRT

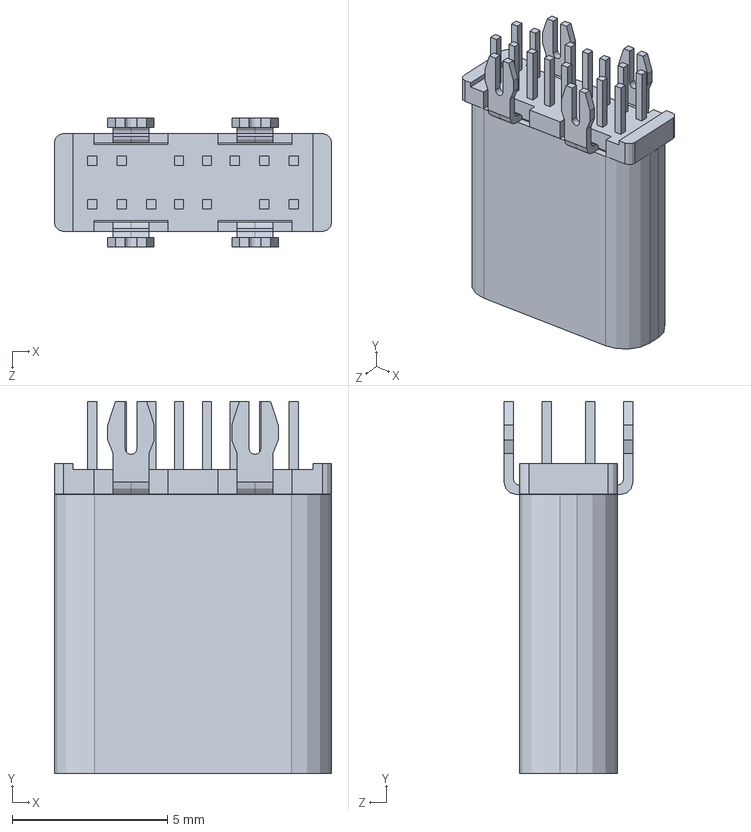
[picture p114: CAD file, 2024-04-08]
Hardware/SW_Project/TYPE-C-14-vertical_H-10mm.SLDPRT
8.95 x 12.0 x 4.16 mm
