oldgerman/SAU-G0/Hardware/Datasheets/连接器/泰科 198181x 连接器/c-1981812-1-b-3d.stp

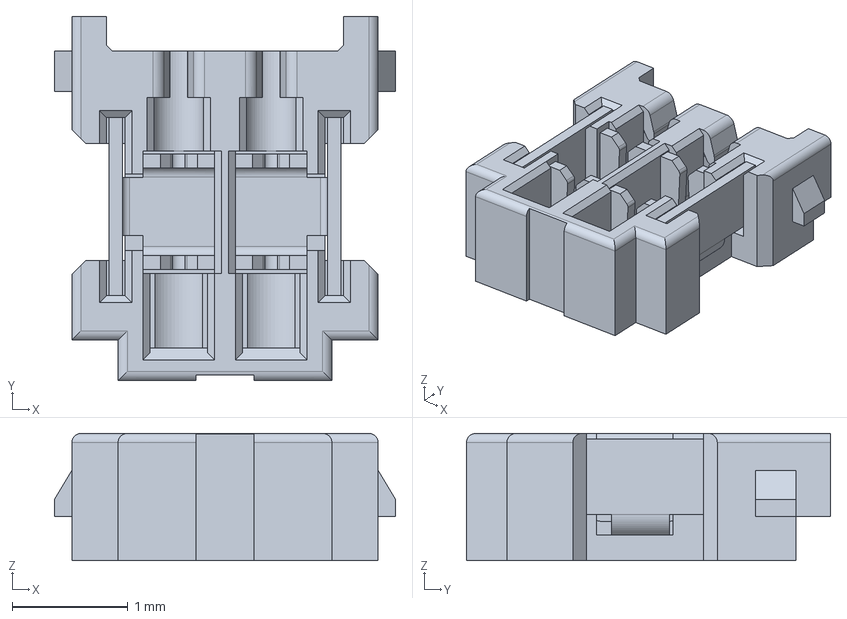
[picture p115: CAD file, 2024-04-08]
Hardware/Datasheets/连接器/泰科 198181x 连接器/c-1981812-1-b-3d.stp
2.95 x 3.15 x 1.10 mm
