oldgerman/SAU-G0/Hardware/SW_Project/AD_STEP_OUT/SAU-G0-EX_AHT-PL.step

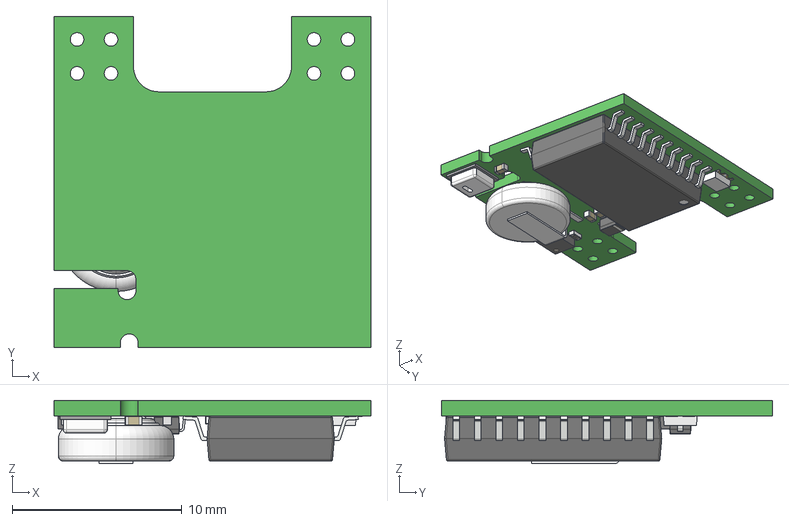
[picture p116: CAD file, 2024-04-08]
Hardware/SW_Project/AD_STEP_OUT/SAU-G0-EX_AHT-PL.step
18.7 x 19.5 x 3.73 mm
WS2812-2020
0402 resistor
0402 cap x 5
DFN-8-1EP_3x2mm_P0.5mm_EP1.75x1.45mm
AHT20 Sensor
0603 resistor
SOD-323
MS621FE-FL11E
SOIC-20 Wide
