oldgerman/SAU-G0/Hardware/SW_Project/DXF_OUT/轻触开关+柔性PCB.DXF

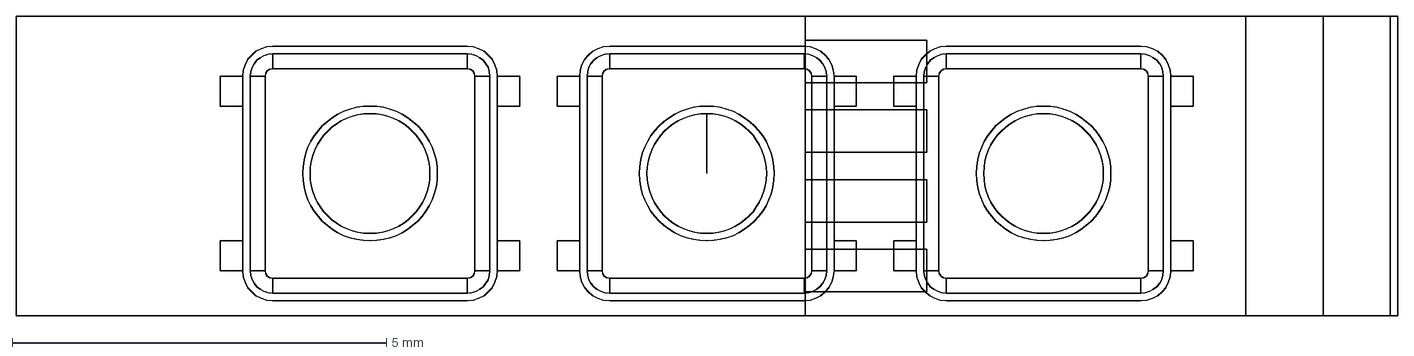
[picture p117: CAD file, 2024-04-08]
Hardware/SW_Project/DXF_OUT/轻触开关+柔性PCB.DXF
18.5 x 4.00 mm
