oldgerman/SAU-G0/Hardware/SW_Project/STEP_OUT/0.66寸_64x48_TOP_FPC背面距离背板1mm.STEP

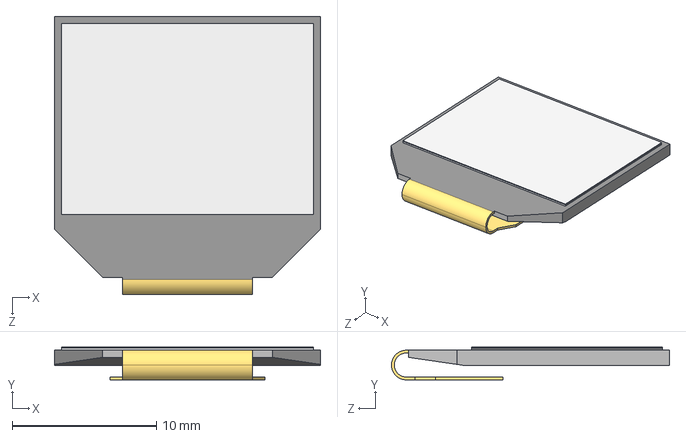
[picture p118: CAD file, 2024-04-08]
Hardware/SW_Project/STEP_OUT/0.66寸_64x48_TOP_FPC背面距离背板1mm.STEP
18.5 x 2.27 x 19.3 mm
