oldgerman/SAU-G0/Hardware/SW_Project/STL_OUT/单个零件/外壳-方案2-PL_盒子.STL

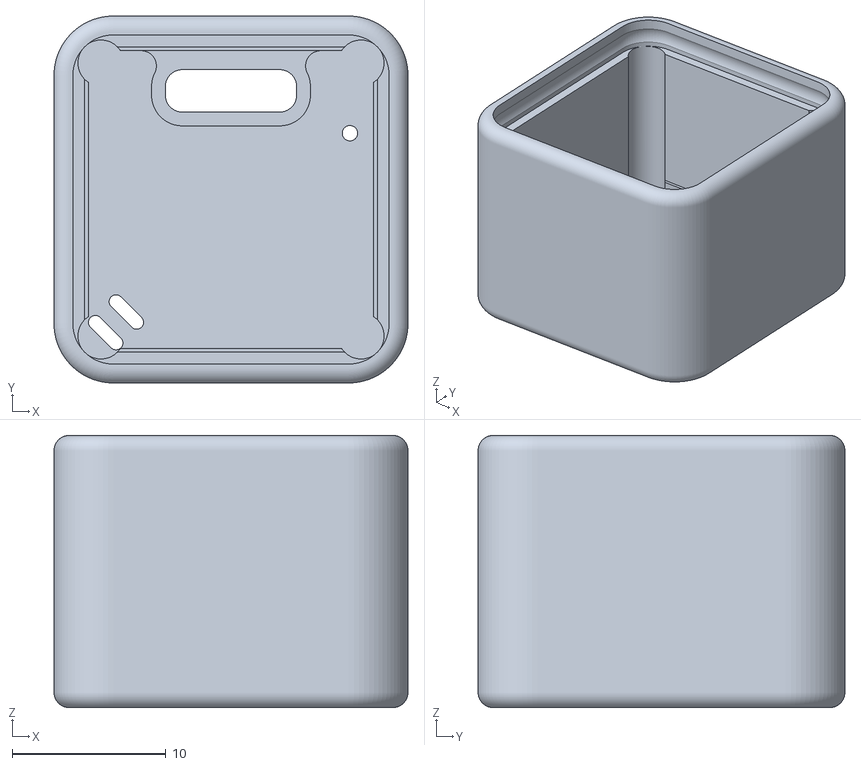
[picture p119: CAD file, 2024-04-08]
Hardware/SW_Project/STL_OUT/单个零件/外壳-方案2-PL_盒子.STL
23.1 x 23.9 x 17.7
