oldgerman/SAU-G0/Hardware/SW_Project/DXF_OUT/Type-c-14p_vertical_H-10mm.DXF

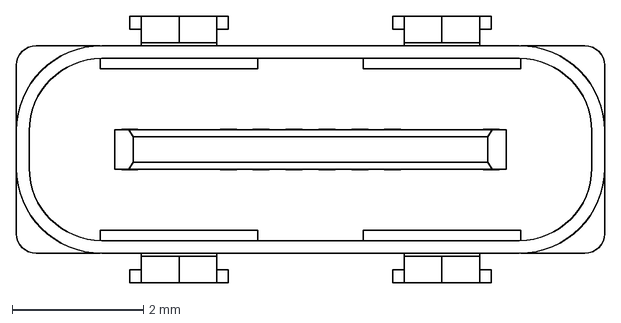
[picture p120: CAD file, 2024-04-08]
Hardware/SW_Project/DXF_OUT/Type-c-14p_vertical_H-10mm.DXF
8.95 x 4.06 mm
