oldgerman/SAU-G0/Hardware/SW_Project/STL_OUT/单个零件/外壳-方案2-GL或PL_盖子.STL

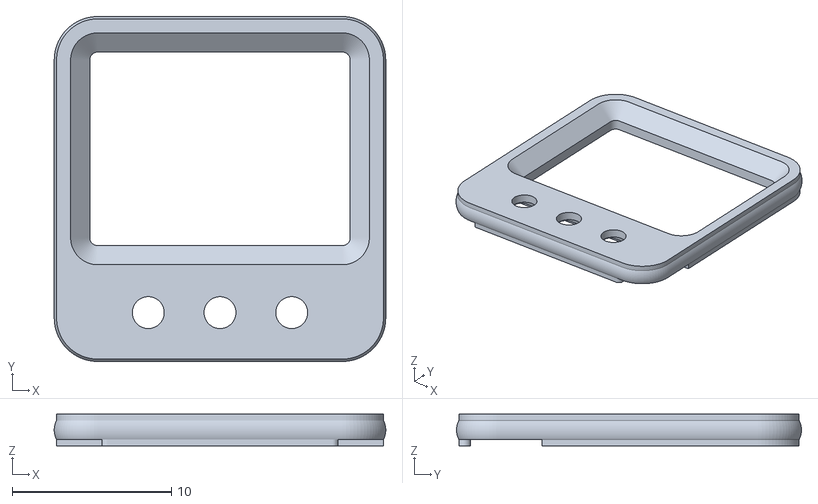
[picture p121: CAD file, 2024-04-08]
Hardware/SW_Project/STL_OUT/单个零件/外壳-方案2-GL或PL_盖子.STL
20.8 x 21.6 x 2.00
