oldgerman/SAU-G0/Hardware/SW_Project/TYPE-C-14-vertical_H-10mm_导出Altium对齐原点.SLDPRT

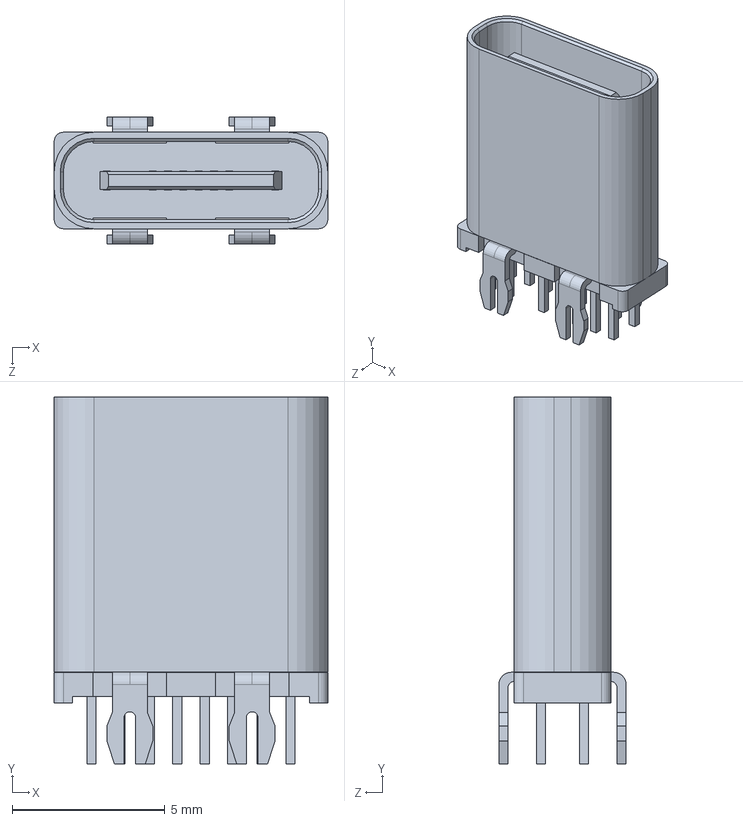
[picture p122: CAD file, 2024-04-08]
Hardware/SW_Project/TYPE-C-14-vertical_H-10mm_导出Altium对齐原点.SLDPRT
8.95 x 12.0 x 4.16 mm
