oldgerman/SAU-G0/Hardware/SW_Project/DXF_OUT/泰科198181x公母装配.DXF

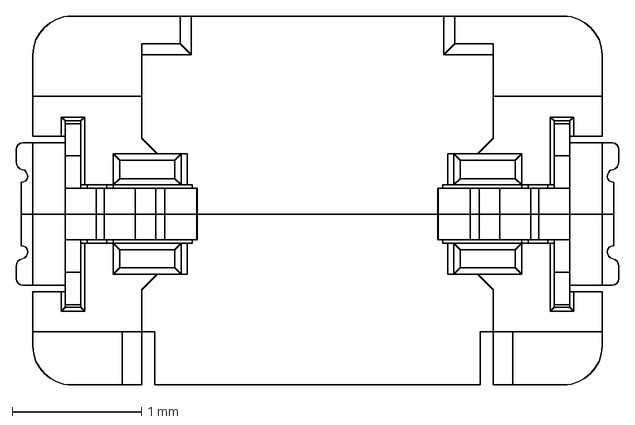
[picture p123: CAD file, 2024-04-08]
Hardware/SW_Project/DXF_OUT/泰科198181x公母装配.DXF
4.66 x 2.85 mm
