oldgerman/SAU-G0/Hardware/SW_Project/2.00mm_2x2_垫板PCB_厚0.8mm.SLDPRT

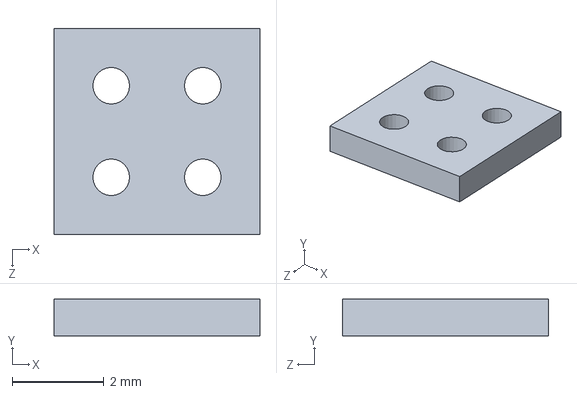
[picture p124: CAD file, 2024-04-08]
Hardware/SW_Project/2.00mm_2x2_垫板PCB_厚0.8mm.SLDPRT
4.50 x 0.8 x 4.50 mm
