oldgerman/SAU-G0/Hardware/SW_Project/STEP_OUT/MS621FE-FL11E.STEP

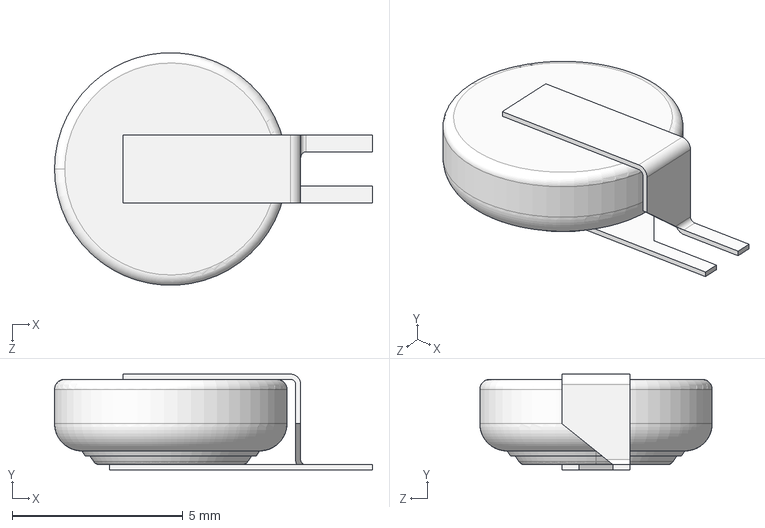
[picture p125: CAD file, 2024-04-08]
Hardware/SW_Project/STEP_OUT/MS621FE-FL11E.STEP
9.30 x 2.80 x 6.79 mm
