oldgerman/SAU-G0/Hardware/SW_Project/1.27mm排母x2.SLDPRT

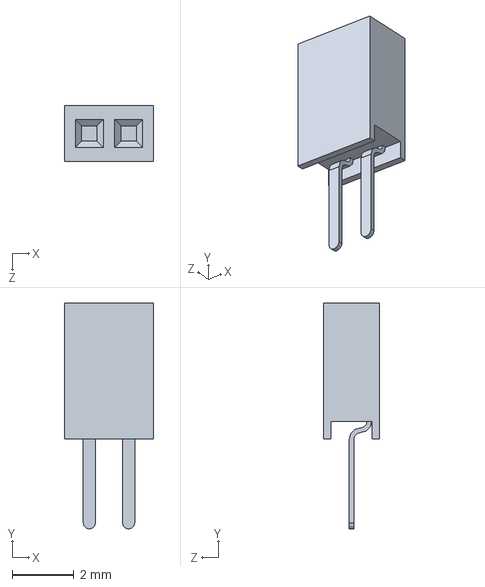
[picture p126: CAD file, 2024-04-08]
Hardware/SW_Project/1.27mm排母x2.SLDPRT
2.86 x 7.30 x 1.80 mm
