oldgerman/SAU-G0/Hardware/SW_Project/STEP_OUT/泰科198181x公母装配-无线.STEP

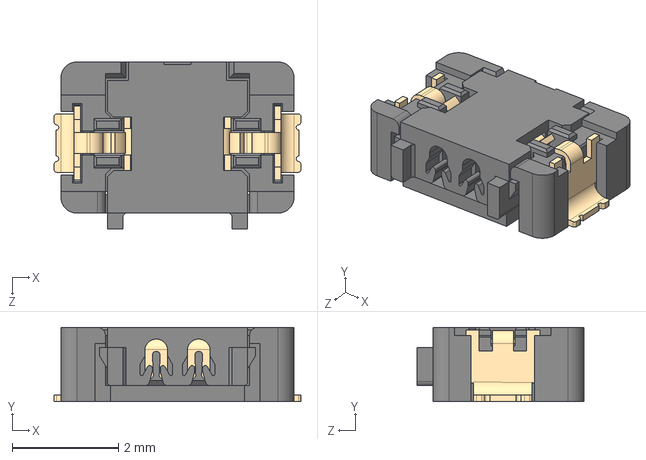
[picture p127: CAD file, 2024-04-08]
Hardware/SW_Project/STEP_OUT/泰科198181x公母装配-无线.STEP
4.66 x 1.40 x 3.15 mm
怍褪1981813-1
怍褪1981812-1
