oldgerman/SAU-G0/Hardware/SW_Project/STEP_OUT/0.66_oled.STEP

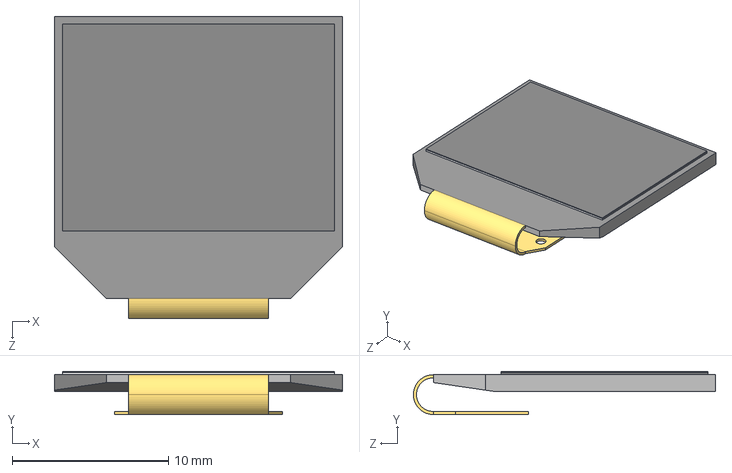
[picture p129: CAD file, 2024-04-08]
Hardware/SW_Project/STEP_OUT/0.66_oled.STEP
18.5 x 2.76 x 19.4 mm
