oldgerman/SAU-G0/Hardware/SW_Project/TYPE-C-塑料内芯.SLDPRT

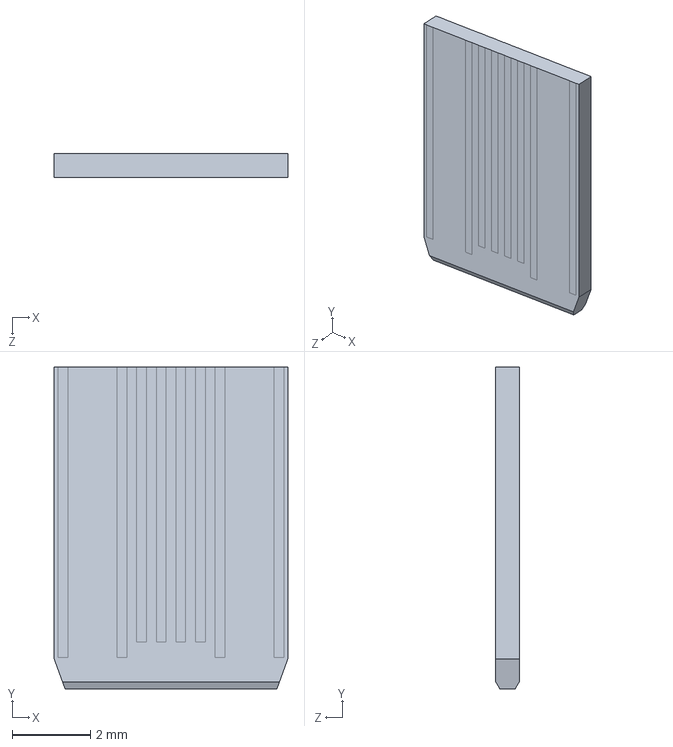
[picture p130: CAD file, 2024-04-08]
Hardware/SW_Project/TYPE-C-塑料内芯.SLDPRT
5.96 x 8.21 x 0.61 mm
