oldgerman/SAU-G0/Hardware/SW_Project/JST_ZH1.5_2P_胶壳.SLDPRT

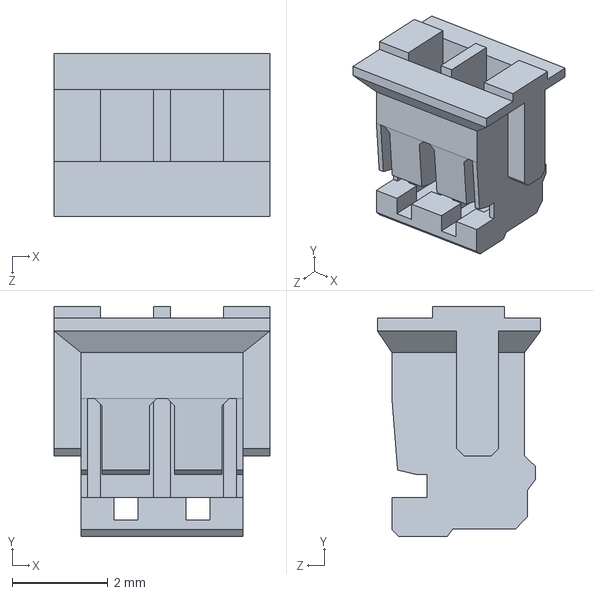
[picture p131: CAD file, 2024-04-08]
Hardware/SW_Project/JST_ZH1.5_2P_胶壳.SLDPRT
4.50 x 4.80 x 3.40 mm
