oldgerman/SAU-G0/Hardware/SW_Project/STEP_OUT/2.0mm排针2x2.STEP

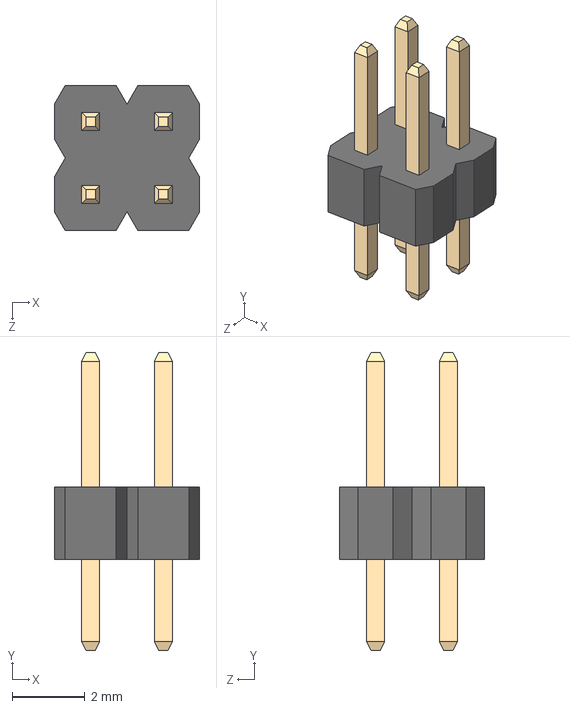
[picture p132: CAD file, 2024-04-08]
Hardware/SW_Project/STEP_OUT/2.0mm排针2x2.STEP
4.00 x 8.20 x 4.00 mm
