oldgerman/SAU-G0/Hardware/SW_Project/外壳-盖子.SLDPRT

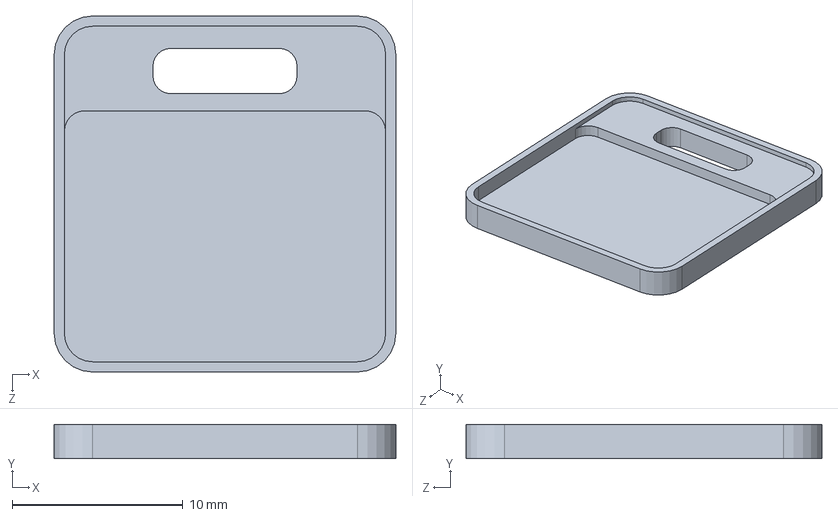
[picture p133: CAD file, 2024-04-08]
Hardware/SW_Project/外壳-盖子.SLDPRT
20.0 x 2.00 x 20.9 mm
