oldgerman/SAU-G0/Hardware/SW_Project/LGA-16_3x3mm_P0.5mm.SLDPRT

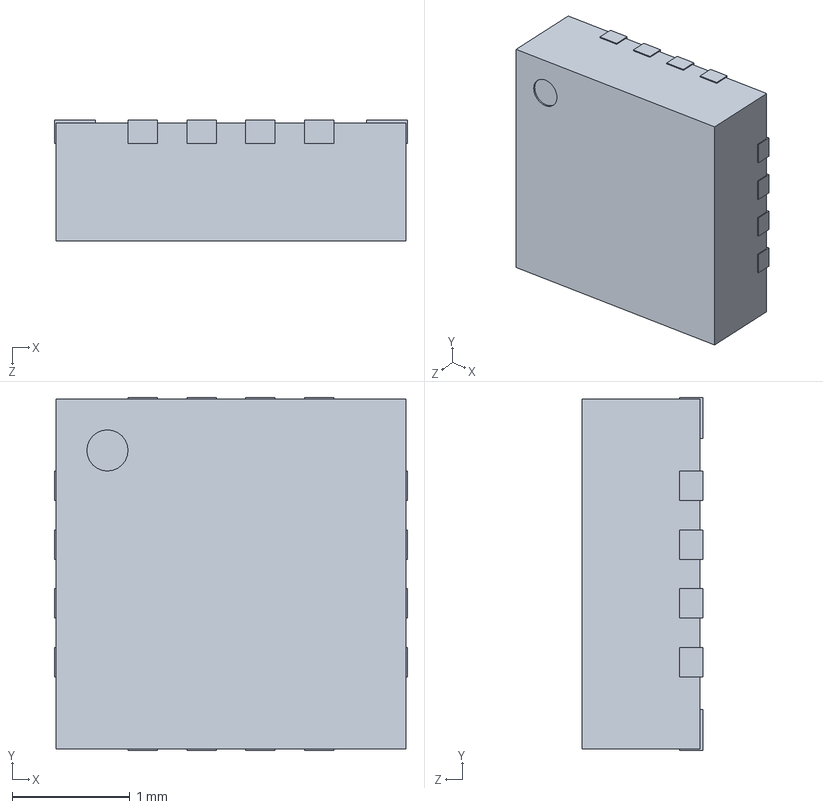
[picture p134: CAD file, 2024-04-08]
Hardware/SW_Project/LGA-16_3x3mm_P0.5mm.SLDPRT
3.00 x 3.00 x 1.02 mm
