oldgerman/SAU-G0/Hardware/SW_Project/2.54mm_母座插针.SLDPRT

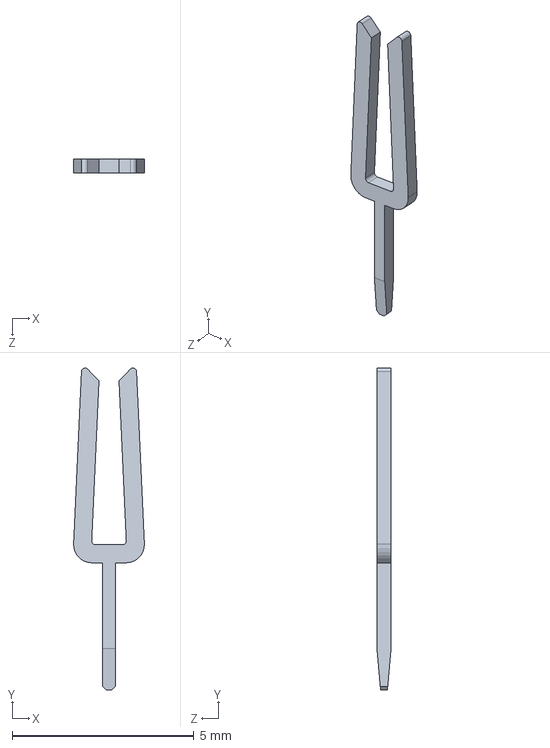
[picture p135: CAD file, 2024-04-08]
Hardware/SW_Project/2.54mm_母座插针.SLDPRT
1.95 x 8.86 x 0.39 mm
