oldgerman/SAU-G0/Hardware/SW_Project/2.00mm_2x2_垫板PCB_厚1.0mm.SLDPRT

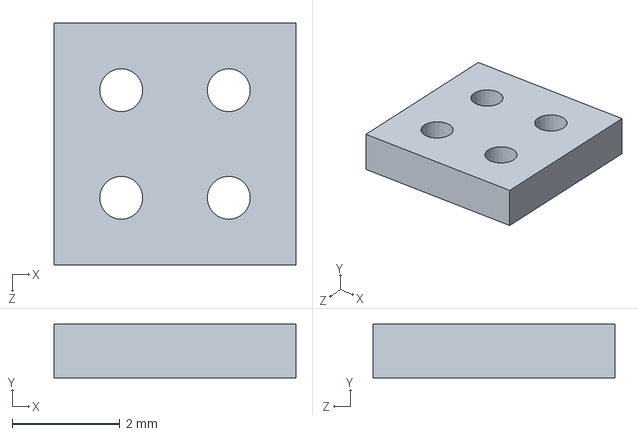
[picture p136: CAD file, 2024-04-08]
Hardware/SW_Project/2.00mm_2x2_垫板PCB_厚1.0mm.SLDPRT
4.50 x 1.00 x 4.50 mm
