oldgerman/SAU-G0/Hardware/SW_Project/外壳-方案2-盖子_LC打印.SLDPRT

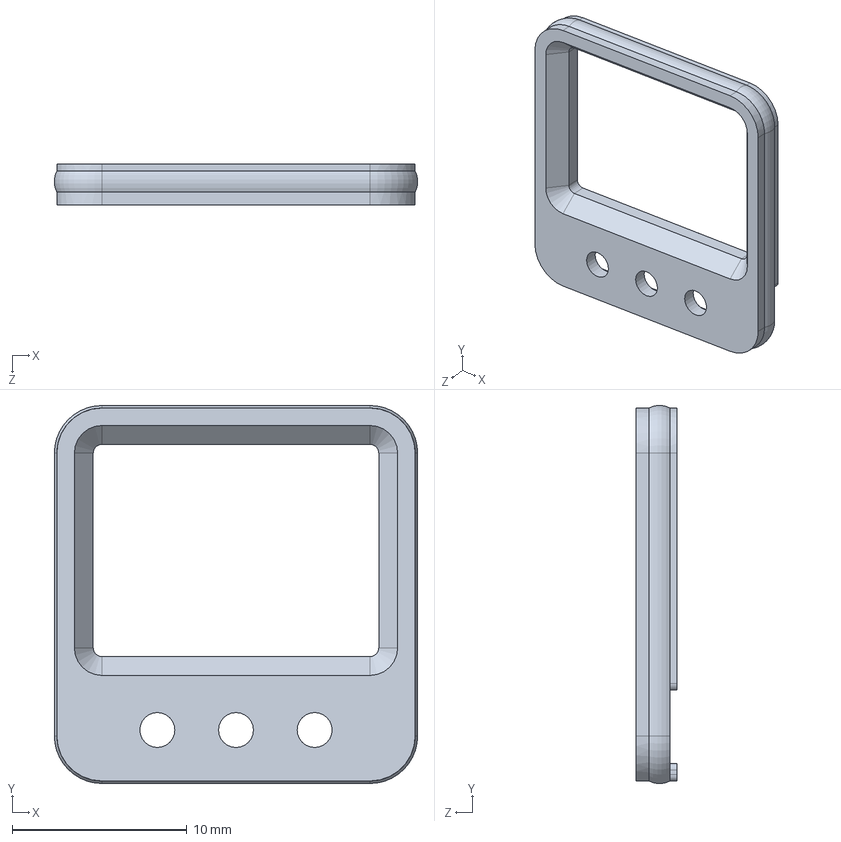
[picture p137: CAD file, 2024-04-08]
Hardware/SW_Project/外壳-方案2-盖子_LC打印.SLDPRT
20.8 x 21.6 x 2.34 mm
