oldgerman/SAU-G0/Hardware/SW_Project/2.00mm母座2x1.SLDPRT

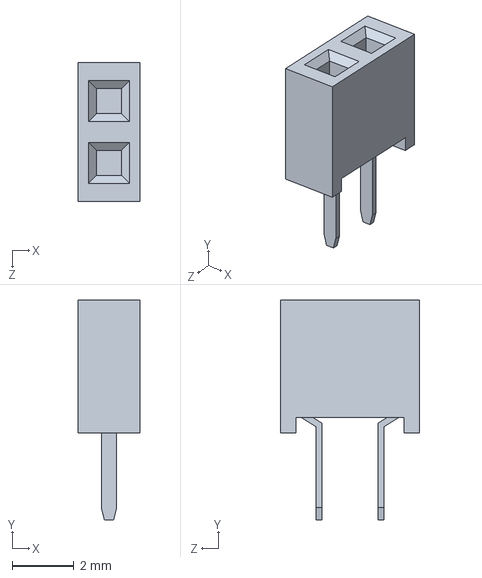
[picture p138: CAD file, 2024-04-08]
Hardware/SW_Project/2.00mm母座2x1.SLDPRT
2.00 x 7.10 x 4.50 mm
