oldgerman/SAU-G0/Hardware/SW_Project/HRO_TYPE-C-31-M-12.SLDPRT

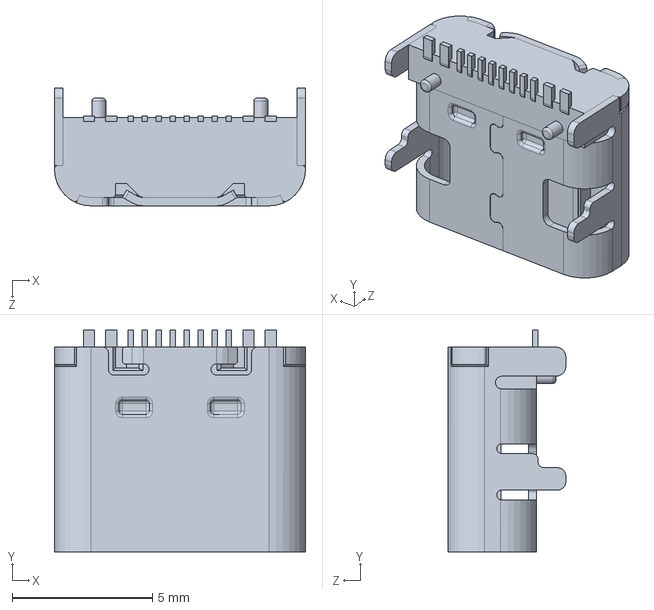
[picture p139: CAD file, 2024-04-08]
Hardware/SW_Project/HRO_TYPE-C-31-M-12.SLDPRT
8.95 x 7.90 x 4.20 mm
