oldgerman/SAU-G0/Hardware/SW_Project/1.27mm排针x2.SLDPRT

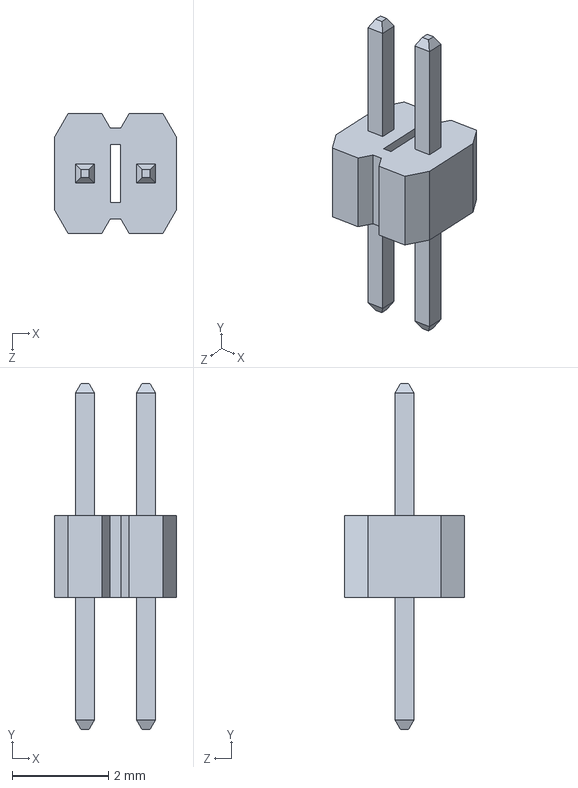
[picture p140: CAD file, 2024-04-08]
Hardware/SW_Project/1.27mm排针x2.SLDPRT
2.54 x 7.20 x 2.50 mm
