oldgerman/SAU-G0/Hardware/SW_Project/32AWG特氟龙7股线-黑.SLDPRT

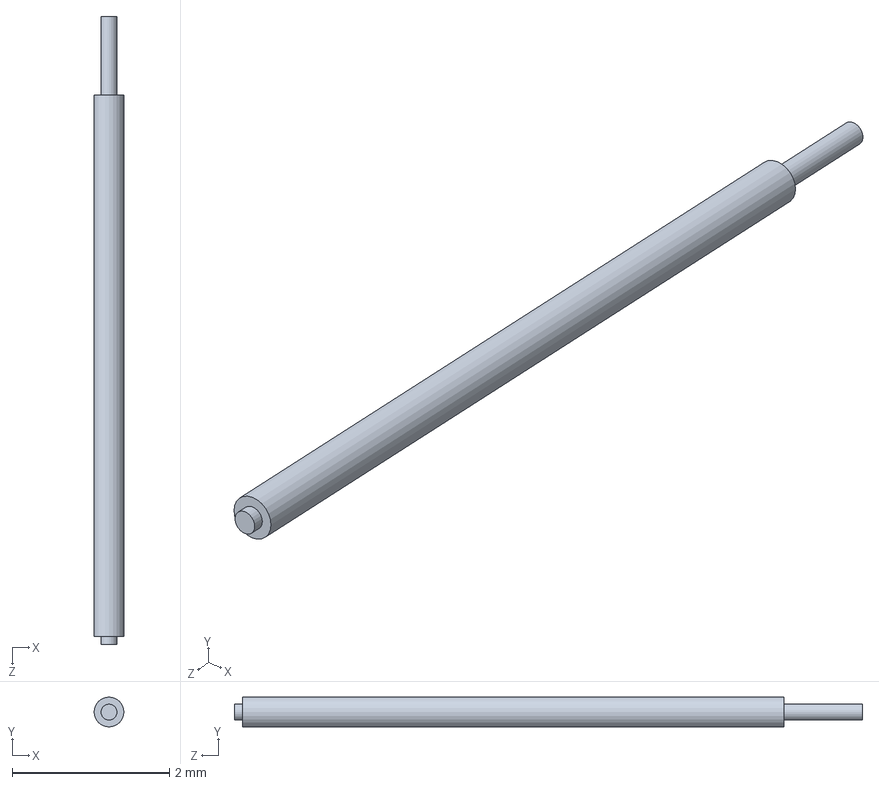
[picture p141: CAD file, 2024-04-08]
Hardware/SW_Project/32AWG特氟龙7股线-黑.SLDPRT
0.38 x 0.38 x 8.00 mm
