oldgerman/SAU-G0/Hardware/SW_Project/AHT20 Sensor.step

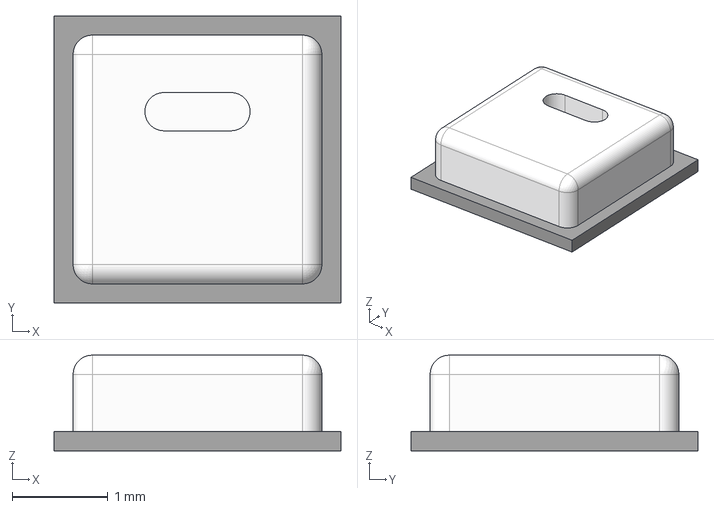
[picture p142: CAD file, 2024-04-08]
Hardware/SW_Project/AHT20 Sensor.step
3.00 x 3.00 x 1.00 mm
