oldgerman/SAU-G0/Hardware/SW_Project/轻触开关3x3.5x1.5_3x4.0x2.0.SLDPRT

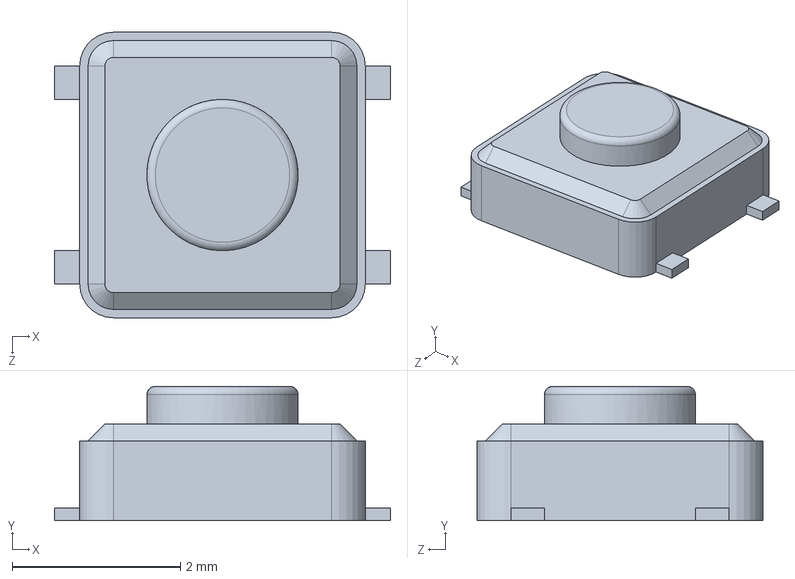
[picture p143: CAD file, 2024-04-08]
Hardware/SW_Project/轻触开关3x3.5x1.5_3x4.0x2.0.SLDPRT
4.00 x 1.60 x 3.40 mm
