oldgerman/SAU-G0/Hardware/SW_Project/外壳.SLDPRT

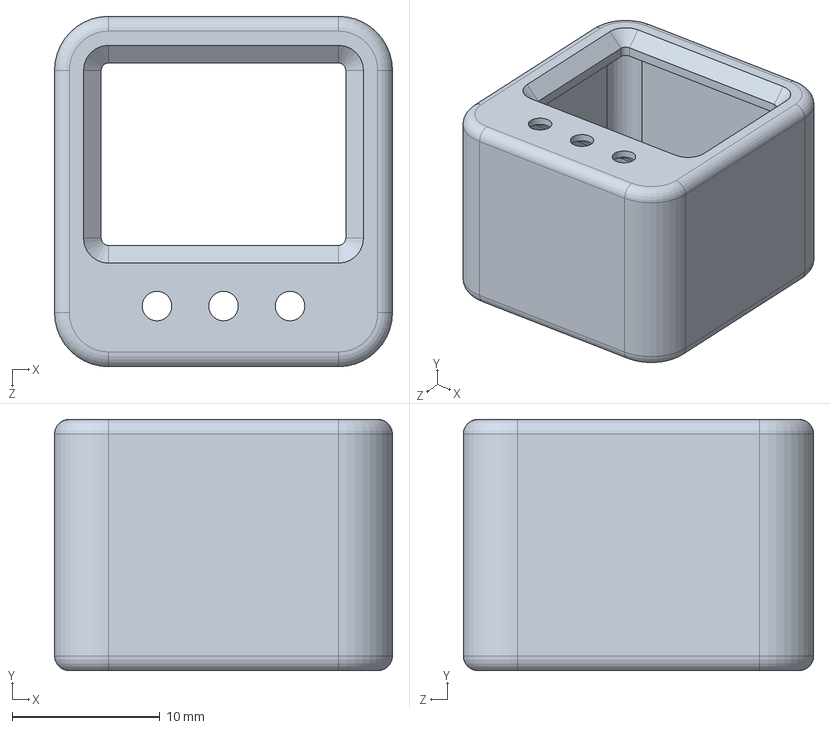
[picture p144: CAD file, 2024-04-08]
Hardware/SW_Project/外壳.SLDPRT
22.9 x 17.0 x 23.7 mm
