oldgerman/SAU-G0/Hardware/SW_Project/2.54x2x1奇怪的.SLDPRT

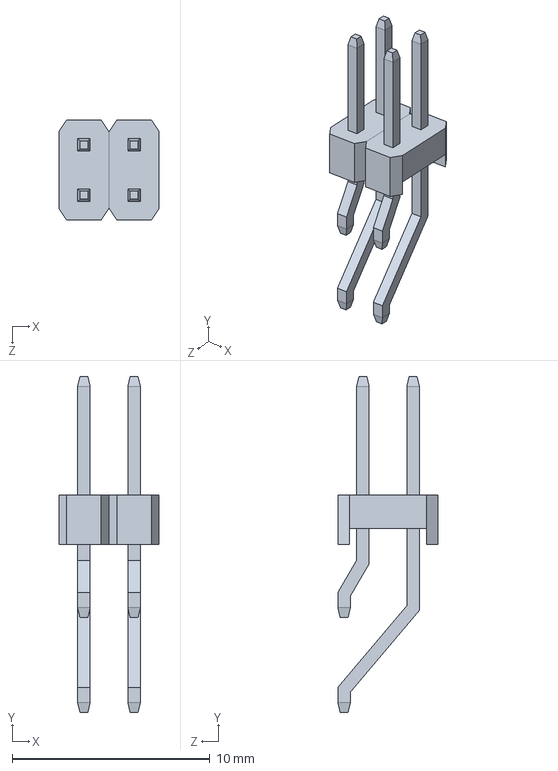
[picture p145: CAD file, 2024-04-08]
Hardware/SW_Project/2.54x2x1奇怪的.SLDPRT
5.08 x 17.0 x 5.08 mm
