oldgerman/SAU-G0/Hardware/SW_Project/PCB.SLDPRT

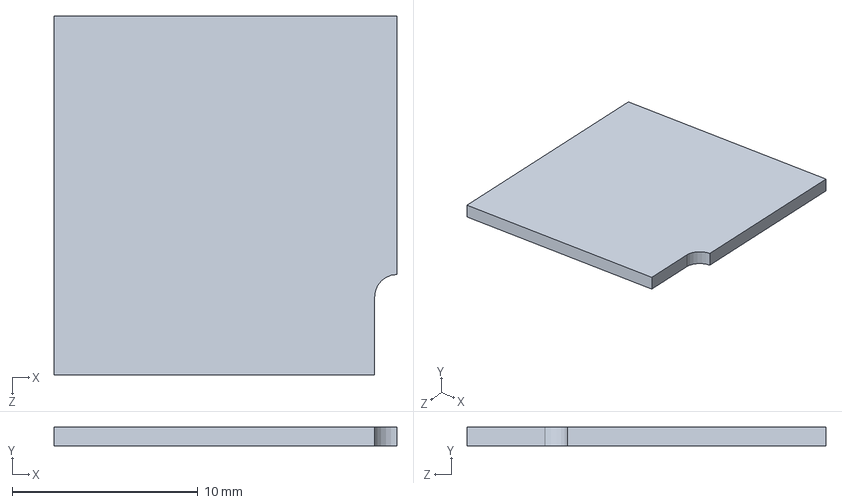
[picture p146: CAD file, 2024-04-08]
Hardware/SW_Project/PCB.SLDPRT
18.5 x 1.00 x 19.3 mm
