oldgerman/SAU-G0/Hardware/SW_Project/2_54_x_4P_Female.STEP

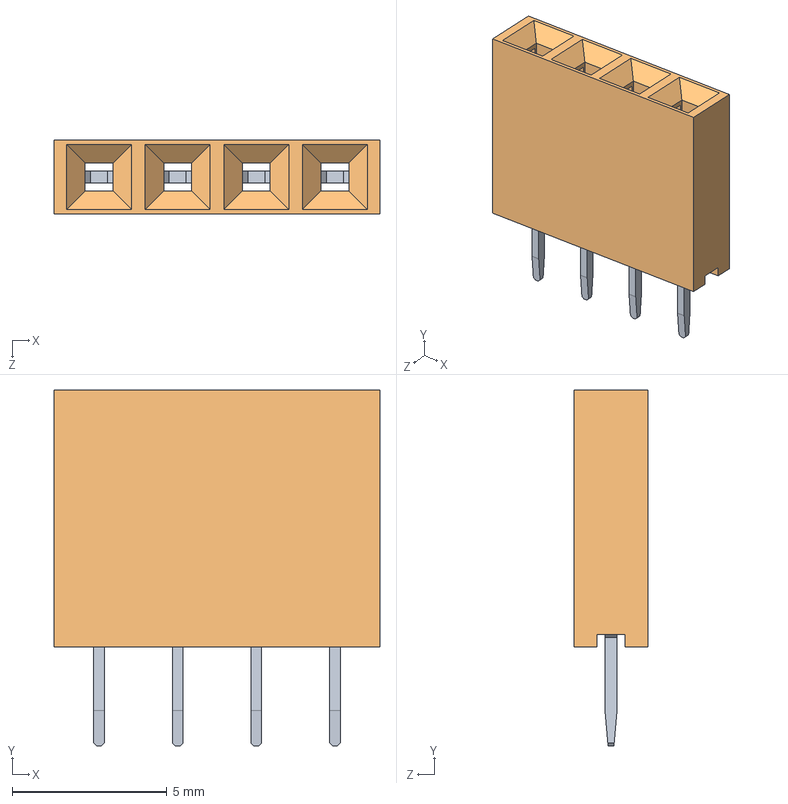
[picture p147: CAD file, 2024-04-08]
Hardware/SW_Project/2_54_x_4P_Female.STEP
10.5 x 11.5 x 2.40 mm
Pitch_x_8_1
Plastic_x_8_1
