oldgerman/SAU-G0/Hardware/SW_Project/2.0mm排针x1.SLDPRT

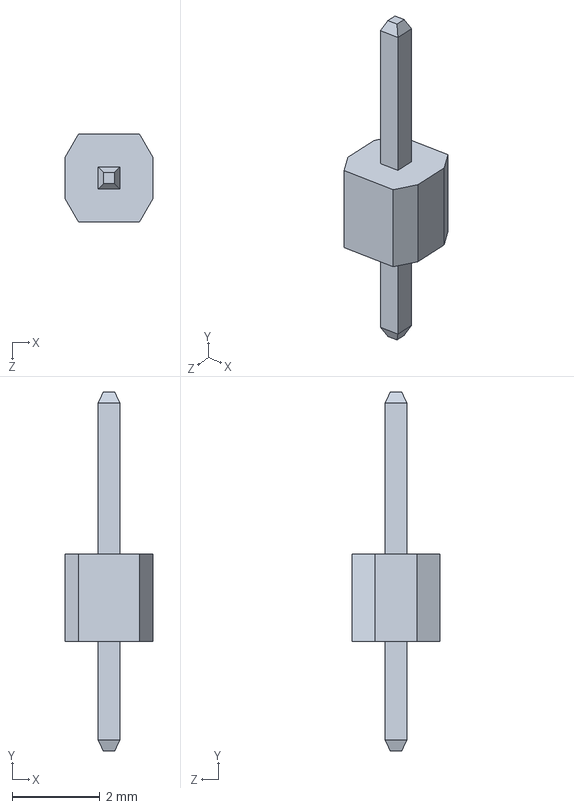
[picture p148: CAD file, 2024-04-08]
Hardware/SW_Project/2.0mm排针x1.SLDPRT
2.00 x 8.20 x 2.00 mm
