oldgerman/SAU-G0/Hardware/SW_Project/UFQFPN-28.step

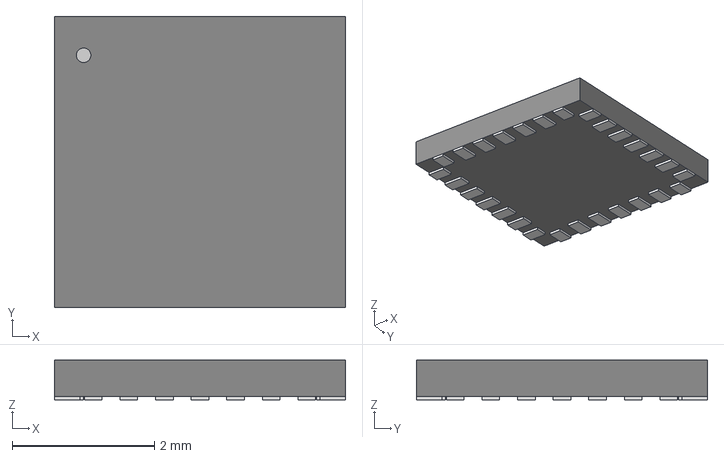
[picture p149: CAD file, 2024-04-08]
Hardware/SW_Project/UFQFPN-28.step
4.09 x 4.09 x 0.561 mm
