oldgerman/SAU-G0/Hardware/SW_Project/sop8.STEP

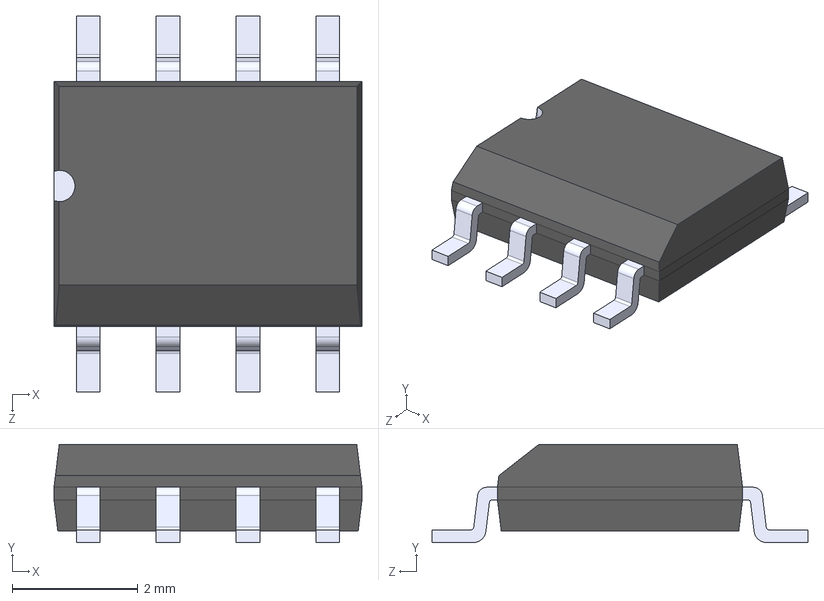
[picture p150: CAD file, 2024-04-08]
Hardware/SW_Project/sop8.STEP
4.90 x 1.56 x 5.98 mm
User Library-sop8_model_pin5to8_sop8 x 8
User Library-sop8_model_sop8_body
