oldgerman/SAU-G0/Hardware/SW_Project/JST_ZH1.5_2P_B2B-ZR-SM4-TF.SLDPRT

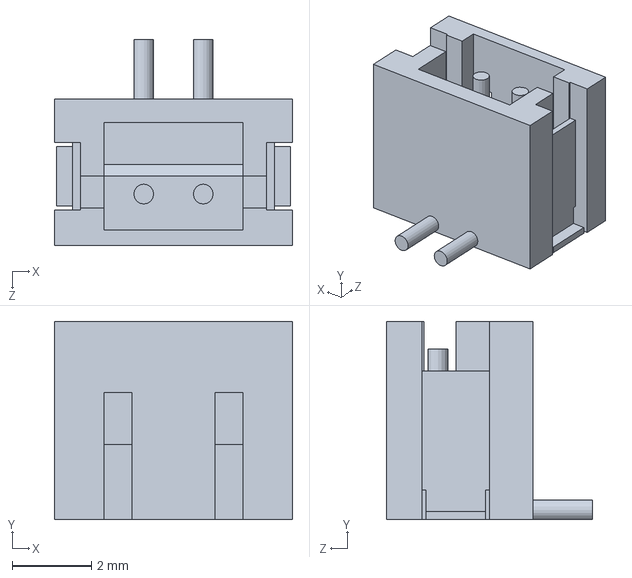
[picture p151: CAD file, 2024-04-08]
Hardware/SW_Project/JST_ZH1.5_2P_B2B-ZR-SM4-TF.SLDPRT
6.00 x 5.00 x 5.20 mm
