oldgerman/SAU-G0/Hardware/Datasheets/RTC/PCF2129/rtc_wiring.png

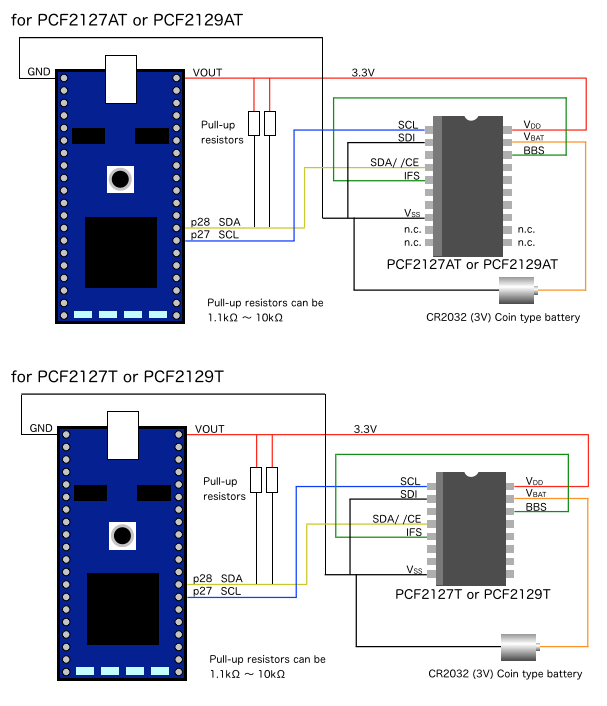
Hardware/Datasheets/RTC/PCF2129/rtc_wiring.png
