oldgerman/SAU-G0/SoftWare/SAU-G031G8U6/Core/Src/i2c.c

/**
  ******************************************************************************
  * @file    i2c.c
  * @brief   This file provides code for the configuration
  *          of the I2C instances.
  ******************************************************************************
  * @attention
  *
  * <h2><center>&copy; Copyright (c) 2022 STMicroelectronics.
  * All rights reserved.</center></h2>
  *
  * This software component is licensed by ST under BSD 3-Clause license,
  * the "License"; You may not use this file except in compliance with the
  * License. You may obtain a copy of the License at:
  *                        opensource.org/licenses/BSD-3-Clause
  *
  ******************************************************************************
  */

/* Includes ------------------------------------------------------------------*/
#include "i2c.h"

/* USER CODE BEGIN 0 */
#include "ee24.hpp"
/* USER CODE END 0 */

I2C_HandleTypeDef hi2c1;
I2C_HandleTypeDef hi2c2;

/* I2C1 init function */
void MX_I2C1_Init(void)
{

  hi2c1.Instance = I2C1;
  hi2c1.Init.Timing = 0x00303D5B;
  hi2c1.Init.OwnAddress1 = 0;
  hi2c1.Init.AddressingMode = I2C_ADDRESSINGMODE_7BIT;
  hi2c1.Init.DualAddressMode = I2C_DUALADDRESS_DISABLE;
  hi2c1.Init.OwnAddress2 = 0;
  hi2c1.Init.OwnAddress2Masks = I2C_OA2_NOMASK;
  hi2c1.Init.GeneralCallMode = I2C_GENERALCALL_DISABLE;
  hi2c1.Init.NoStretchMode = I2C_NOSTRETCH_DISABLE;
  if (HAL_I2C_Init(&hi2c1) != HAL_OK)
  {
    Error_Handler();
  }
  /** Configure Analogue filter
  */
  if (HAL_I2CEx_ConfigAnalogFilter(&hi2c1, I2C_ANALOGFILTER_ENABLE) != HAL_OK)
  {
    Error_Handler();
  }
  /** Configure Digital filter
  */
  if (HAL_I2CEx_ConfigDigitalFilter(&hi2c1, 0) != HAL_OK)
  {
    Error_Handler();
  }
}
/* I2C2 init function */
void MX_I2C2_Init(void)
{

  hi2c2.Instance = I2C2;
  hi2c2.Init.Timing = 0x00303D5B;
  hi2c2.Init.OwnAddress1 = 0;
  hi2c2.Init.AddressingMode = I2C_ADDRESSINGMODE_7BIT;
  hi2c2.Init.DualAddressMode = I2C_DUALADDRESS_DISABLE;
  hi2c2.Init.OwnAddress2 = 0;
  hi2c2.Init.OwnAddress2Masks = I2C_OA2_NOMASK;
  hi2c2.Init.GeneralCallMode = I2C_GENERALCALL_DISABLE;
  hi2c2.Init.NoStretchMode = I2C_NOSTRETCH_DISABLE;
  if (HAL_I2C_Init(&hi2c2) != HAL_OK)
  {
    Error_Handler();
  }
  /** Configure Analogue filter
  */
  if (HAL_I2CEx_ConfigAnalogFilter(&hi2c2, I2C_ANALOGFILTER_ENABLE) != HAL_OK)
  {
    Error_Handler();
  }
  /** Configure Digital filter
  */
  if (HAL_I2CEx_ConfigDigitalFilter(&hi2c2, 0) != HAL_OK)
  {
    Error_Handler();
  }
}

void HAL_I2C_MspInit(I2C_HandleTypeDef* i2cHandle)
{

  GPIO_InitTypeDef GPIO_InitStruct = {0};
  if(i2cHandle->Instance==I2C1)
  {
  /* USER CODE BEGIN I2C1_MspInit 0 */
	if(exChangeI2C1Pins){
		__HAL_RCC_GPIOB_CLK_ENABLE();
		/**I2C1 GPIO Configuration
		PB6     ------> I2C1_SCL
		PB7     ------> I2C1_SDA
		 */
		GPIO_InitStruct.Pin = GPIO_PIN_6|GPIO_PIN_7;
		GPIO_InitStruct.Mode = GPIO_MODE_AF_OD;
		GPIO_InitStruct.Pull = GPIO_NOPULL;
		GPIO_InitStruct.Speed = GPIO_SPEED_FREQ_LOW;
		GPIO_InitStruct.Alternate = GPIO_AF6_I2C1;
		HAL_GPIO_Init(GPIOB, &GPIO_InitStruct);

		/* Peripheral clock enable */
		__HAL_RCC_I2C1_CLK_ENABLE();
		return;
	}
  /* USER CODE END I2C1_MspInit 0 */

    __HAL_RCC_GPIOB_CLK_ENABLE();
    /**I2C1 GPIO Configuration
    PB7     ------> I2C1_SDA
    PB8     ------> I2C1_SCL
    */
    GPIO_InitStruct.Pin = SDA1_Pin|SCL1_Pin;
    GPIO_InitStruct.Mode = GPIO_MODE_AF_OD;
    GPIO_InitStruct.Pull = GPIO_NOPULL;
    GPIO_InitStruct.Speed = GPIO_SPEED_FREQ_LOW;
    GPIO_InitStruct.Alternate = GPIO_AF6_I2C1;
    HAL_GPIO_Init(GPIOB, &GPIO_InitStruct);

    /* I2C1 clock enable */
    __HAL_RCC_I2C1_CLK_ENABLE();
  }
  else if(i2cHandle->Instance==I2C2)
  {
    __HAL_RCC_GPIOA_CLK_ENABLE();
    /**I2C2 GPIO Configuration
    PA11 [PA9]     ------> I2C2_SCL
    PA12 [PA10]     ------> I2C2_SDA
    */
    GPIO_InitStruct.Pin = SCL2_Pin|SDA2_Pin;
    GPIO_InitStruct.Mode = GPIO_MODE_AF_OD;
    GPIO_InitStruct.Pull = GPIO_NOPULL;
    GPIO_InitStruct.Speed = GPIO_SPEED_FREQ_LOW;
    GPIO_InitStruct.Alternate = GPIO_AF6_I2C2;
    HAL_GPIO_Init(GPIOA, &GPIO_InitStruct);

    /* I2C2 clock enable */
    __HAL_RCC_I2C2_CLK_ENABLE();
  }
}

void HAL_I2C_MspDeInit(I2C_HandleTypeDef* i2cHandle)
{

  if(i2cHandle->Instance==I2C1)
  {
    /* Peripheral clock disable */
    __HAL_RCC_I2C1_CLK_DISABLE();

    /**I2C1 GPIO Configuration
    PB7     ------> I2C1_SDA
    PB8     ------> I2C1_SCL
    */
    HAL_GPIO_DeInit(SDA1_GPIO_Port, SDA1_Pin);

    HAL_GPIO_DeInit(SCL1_GPIO_Port, SCL1_Pin);

  }
  else if(i2cHandle->Instance==I2C2)
  {
    /* Peripheral clock disable */
    __HAL_RCC_I2C2_CLK_DISABLE();

    /**I2C2 GPIO Configuration
    PA11 [PA9]     ------> I2C2_SCL
    PA12 [PA10]     ------> I2C2_SDA
    */
    HAL_GPIO_DeInit(SCL2_GPIO_Port, SCL2_Pin);

    HAL_GPIO_DeInit(SDA2_GPIO_Port, SDA2_Pin);

  }
}

/************************ (C) COPYRIGHT STMicroelectronics *****END OF FILE****/
