oldgerman/SAU-G0/SoftWare/SAU-G031G8U6/USER/BSP/IRQ.h

/*
 * Irqs.h
 *
 *  Created on: 30 May 2020
 *      Author: Ralim
 *      Modify:OldGerman
 */

#ifndef BSP_MINIWARE_IRQ_H_
#define BSP_MINIWARE_IRQ_H_

#include "BSP.h"
#include "I2C_Wrapper.h"
#include "main.h"

#ifdef __cplusplus
extern "C" {
#endif

void HAL_GPIO_EXTI_Falling_Callback(uint16_t GPIO_Pin);	//检测片外RTC中断的回调函数

extern volatile bool intFromRTC;

//extern bool ADC_Injected_Callback_Mark;	//ADC HAL_ADCEx_InjectedConvCpltCallback标记

//以下对HAL的__weak回调函数重写
/*非阻塞模式下的回调函数：
 * 也就是说只有调用FRToI2C的非阻塞API才会调用这些回调函数，使用阻塞API是不会有这些回调函数的
HAL_I2C_ErrorCallback();
HAL_I2C_MasterTxCpltCallback()
HAL_I2C_MasterRxCpltCallback()；
HAL_I2C_MemTxCpltCallback()；
HAL_I2C_MemRxCpltCallback()；
 */

//void HAL_I2C_ErrorCallback(I2C_HandleTypeDef *hi2c);
//void HAL_I2C_AbortCpltCallback(I2C_HandleTypeDef *hi2c);
//void HAL_I2C_MasterTxCpltCallback(I2C_HandleTypeDef *hi2c);
//void HAL_I2C_MasterRxCpltCallback(I2C_HandleTypeDef *hi2c);
//void HAL_I2C_MemTxCpltCallback(I2C_HandleTypeDef *hi2c);
//void HAL_I2C_MemRxCpltCallback(I2C_HandleTypeDef *hi2c);

//void HAL_GPIO_EXTI_Callback(uint16_t);
//void HAL_ADCEx_InjectedConvCpltCallback(ADC_HandleTypeDef *hadc);
//void HAL_ADC_ConvCpltCallback(ADC_HandleTypeDef *hadc);
//void HAL_ADC_ConvHalfCpltCallback(ADC_HandleTypeDef *hadc);
#ifdef __cplusplus
}
#endif
#endif /* BSP_MINIWARE_IRQ_H_ */
